tebl/BulkyModem/faceplates/BulkyModem Terminal FP3/README.md

# BulkyModem Terminal FP3
This is a faceplate, an inherently optional part of any build as it does not actually contain any active components. This faceplate mounts on the **front** of the device, and it is compatible with the following main projects:
- [BulkyModem Terminal](https://github.com/tebl/BulkyModem/tree/main/BulkyModem%20Terminal)

It currently looks like this:
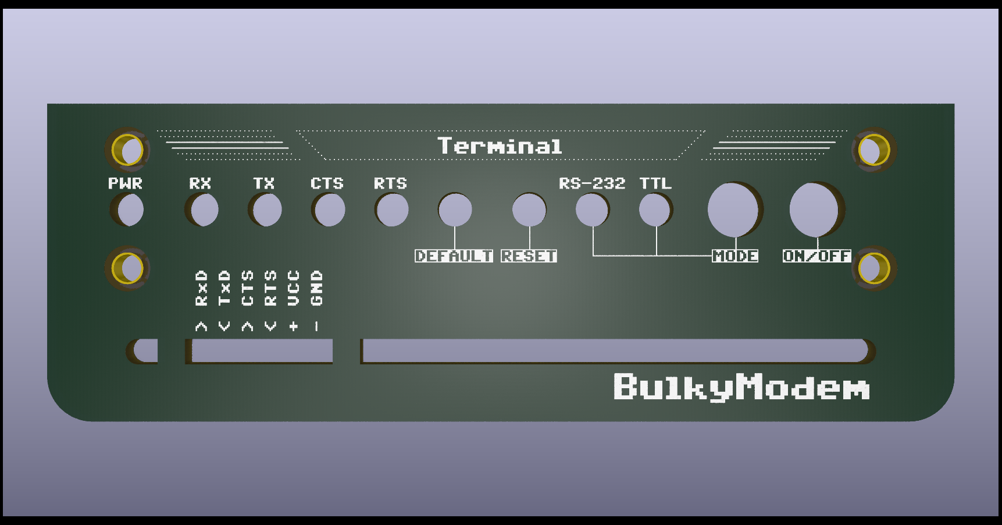
[picture p60: gallery/BulkyModem Terminal FP3.png]
Preview
