tebl/BulkyModem/gallery/20230408_013329.jpg

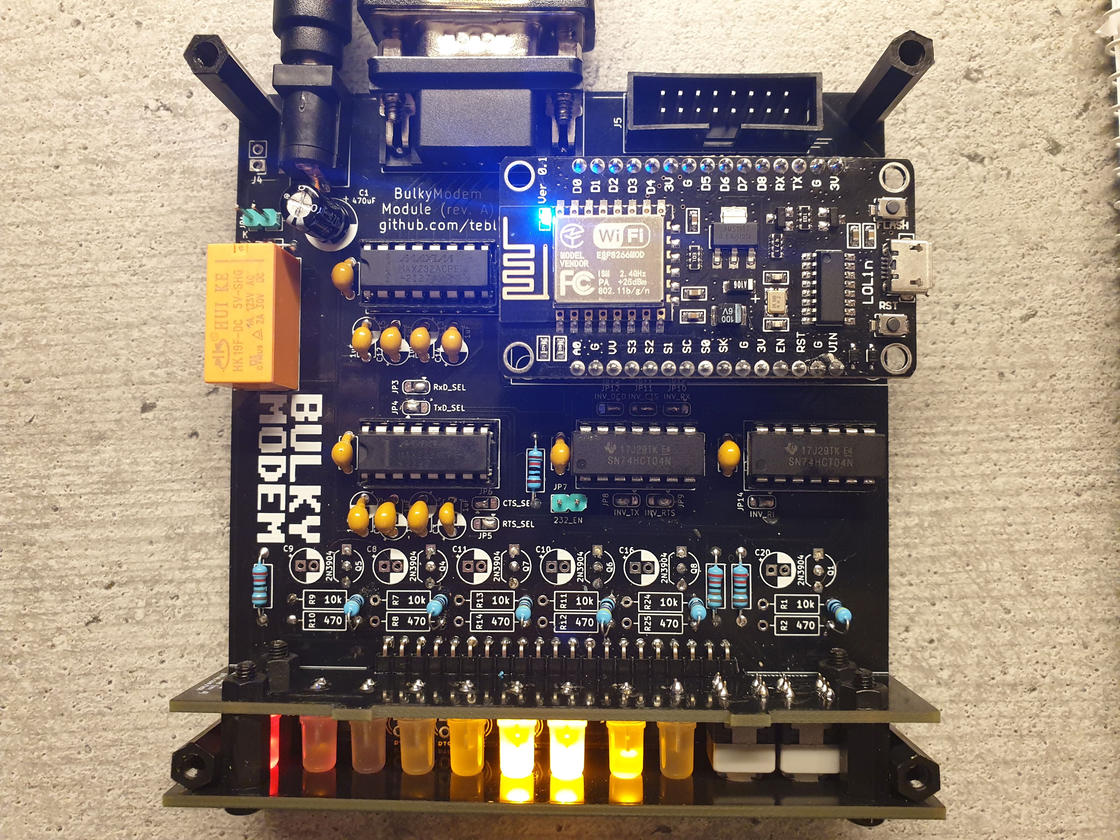
gallery/20230408_013329.jpg
