tebl/BulkyModem/gallery/20240408_024902.jpg

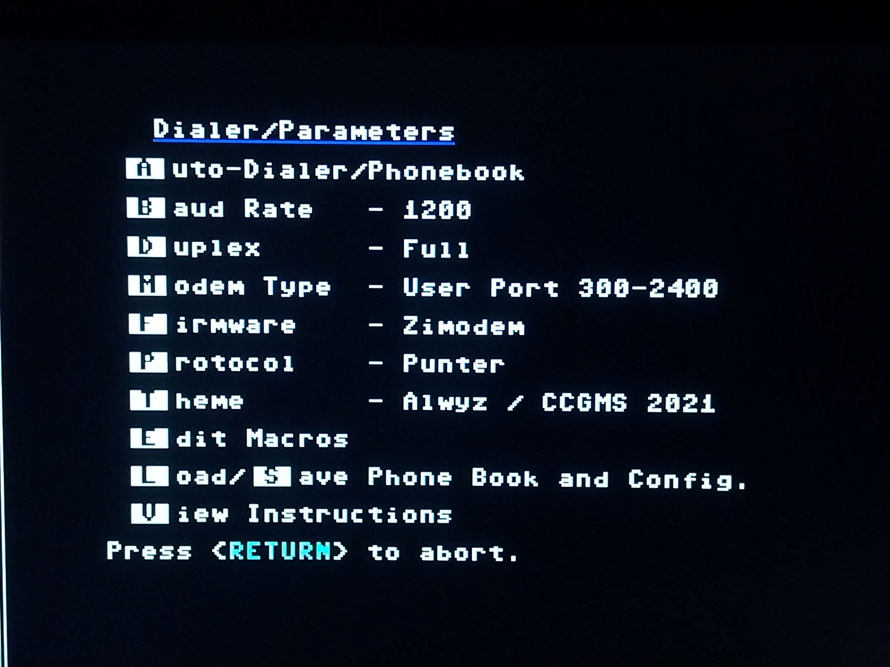
gallery/20240408_024902.jpg
