tebl/BulkyModem/gallery/20240408_025356.jpg

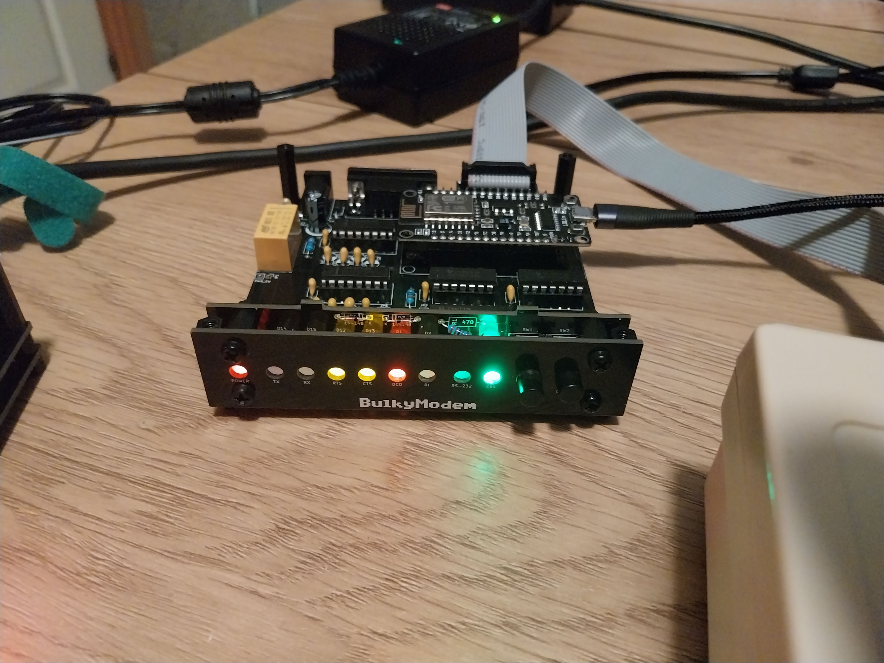
gallery/20240408_025356.jpg
