tebl/BulkyModem/gallery/20240408_030150.jpg

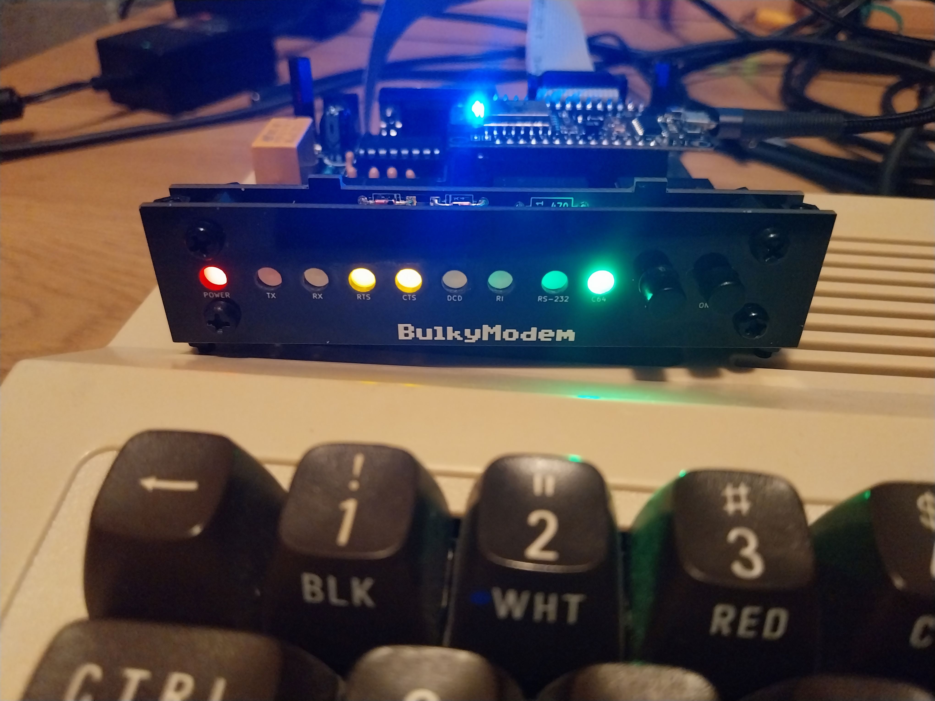
gallery/20240408_030150.jpg
