tebl/BulkyModem/gallery/20240408_030332.jpg

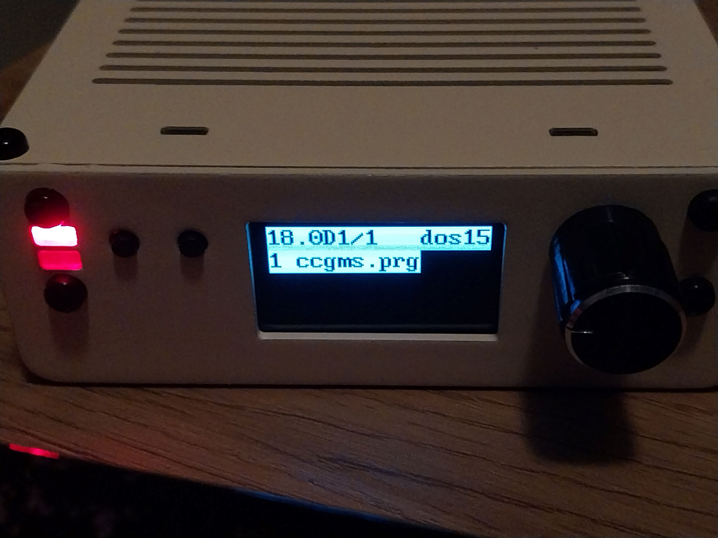
gallery/20240408_030332.jpg
