tebl/BulkyModem/gallery/20240408_030412.jpg

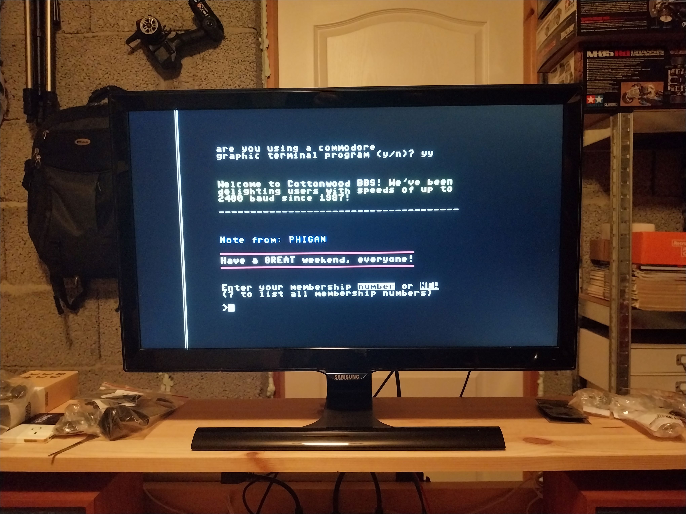
gallery/20240408_030412.jpg
