tebl/BulkyModem/gallery/20240409_003450.jpg

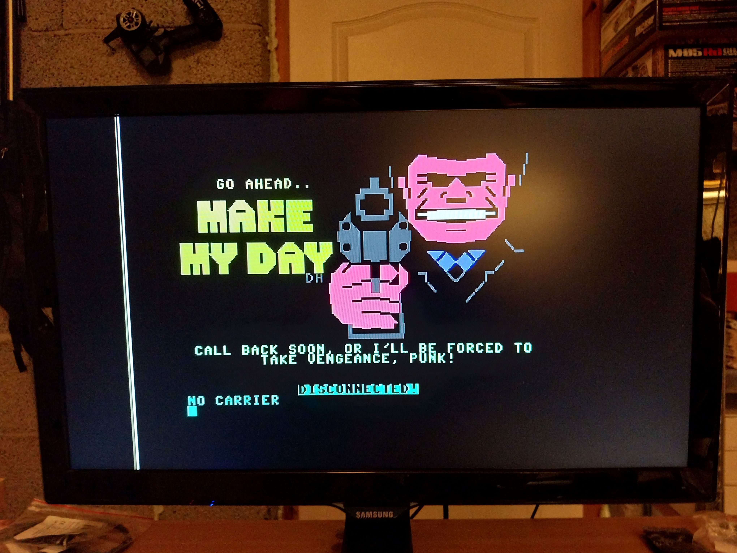
gallery/20240409_003450.jpg
