tebl/BulkyModem/gallery/20240411_001839.jpg

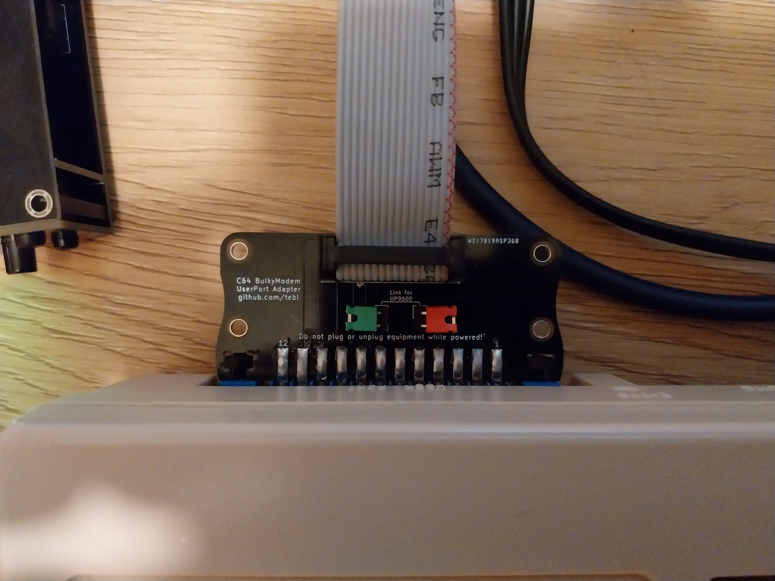
gallery/20240411_001839.jpg
