tebl/BulkyModem/gallery/20240411_020940.jpg

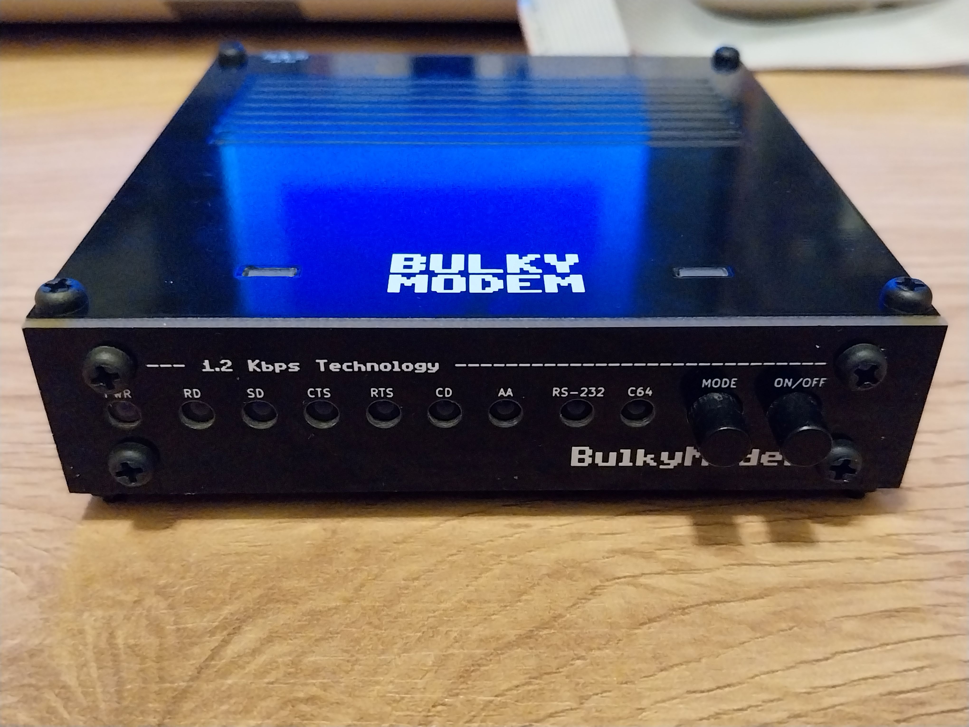
gallery/20240411_020940.jpg
