tebl/BulkyModem/gallery/20240411_020946.jpg

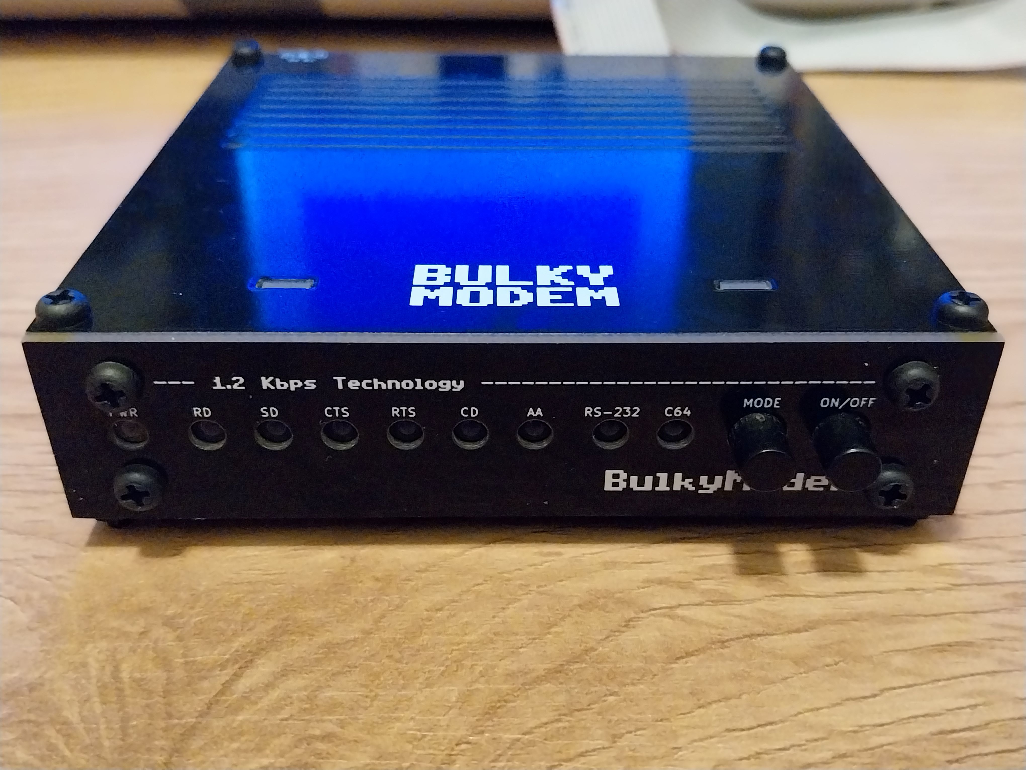
gallery/20240411_020946.jpg
