tebl/BulkyModem/gallery/20240411_021111.jpg

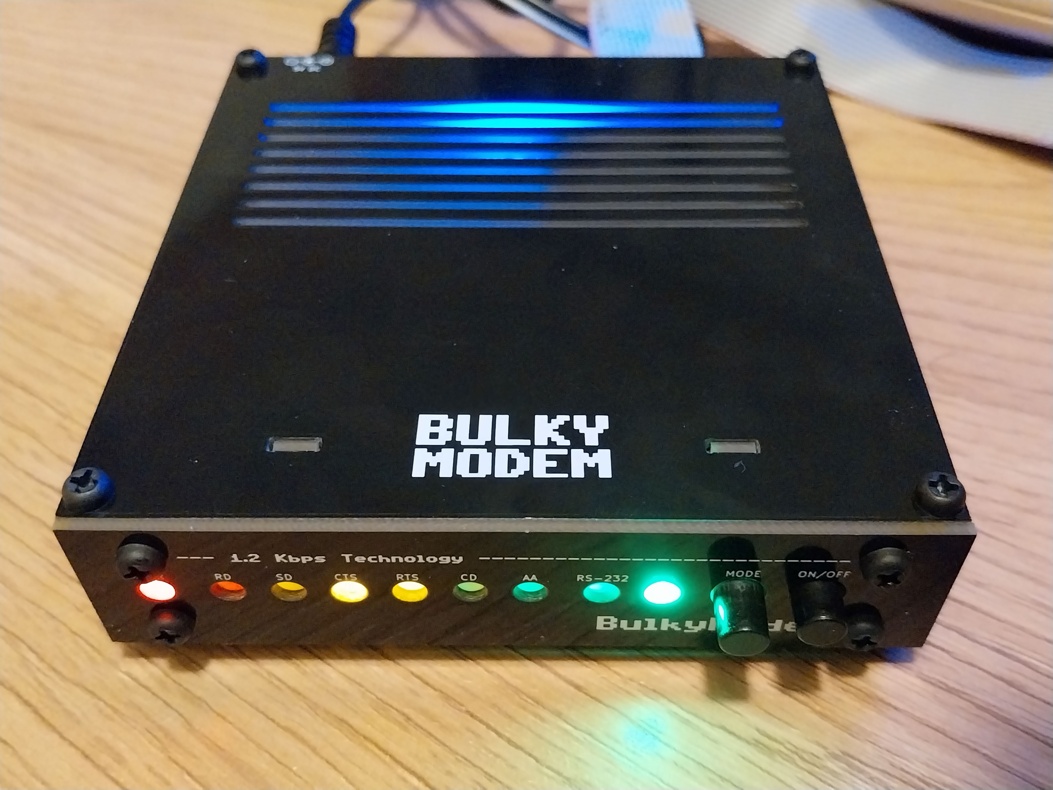
gallery/20240411_021111.jpg
