tebl/BulkyModem/gallery/20240531_021321.jpg

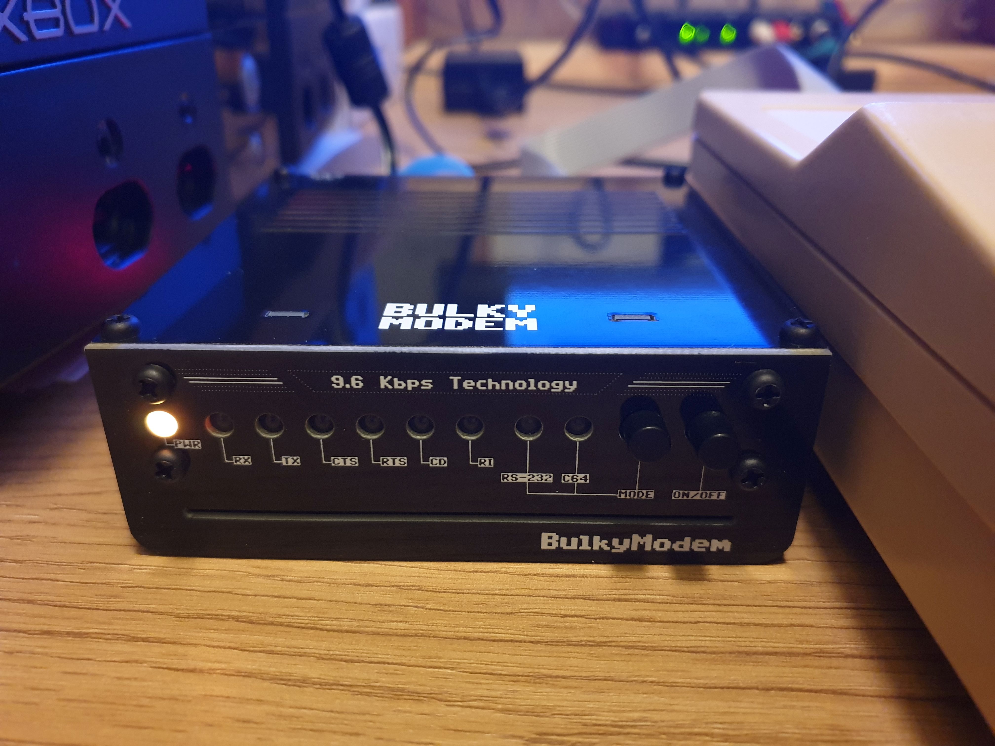
gallery/20240531_021321.jpg
