tebl/BulkyModem/gallery/20240531_021749.jpg

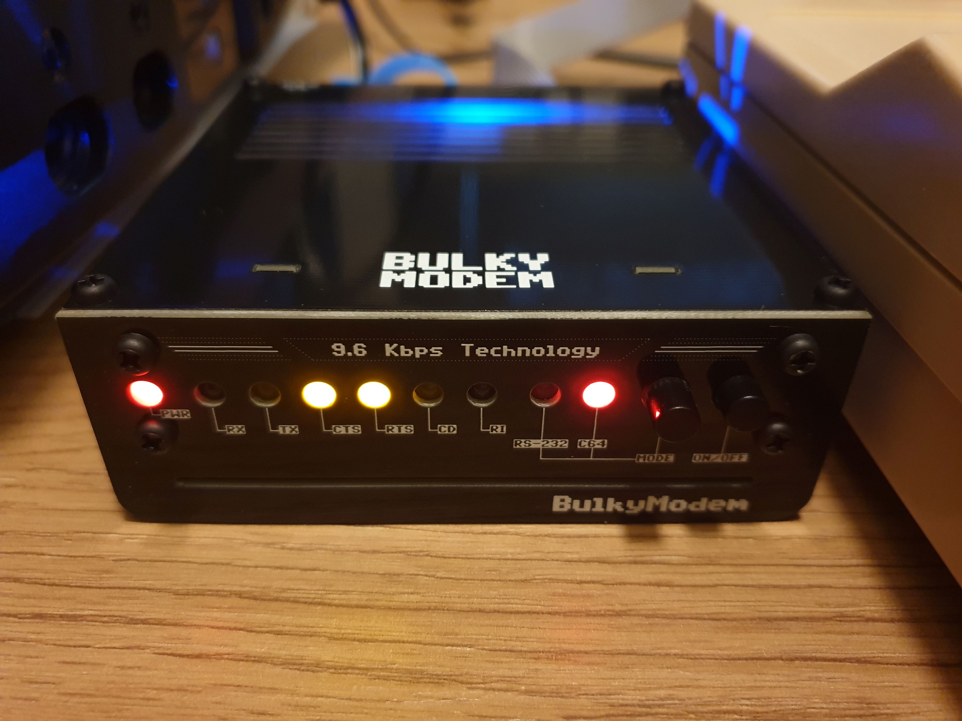
gallery/20240531_021749.jpg
