tebl/BulkyModem/gallery/20240626_021226.jpg

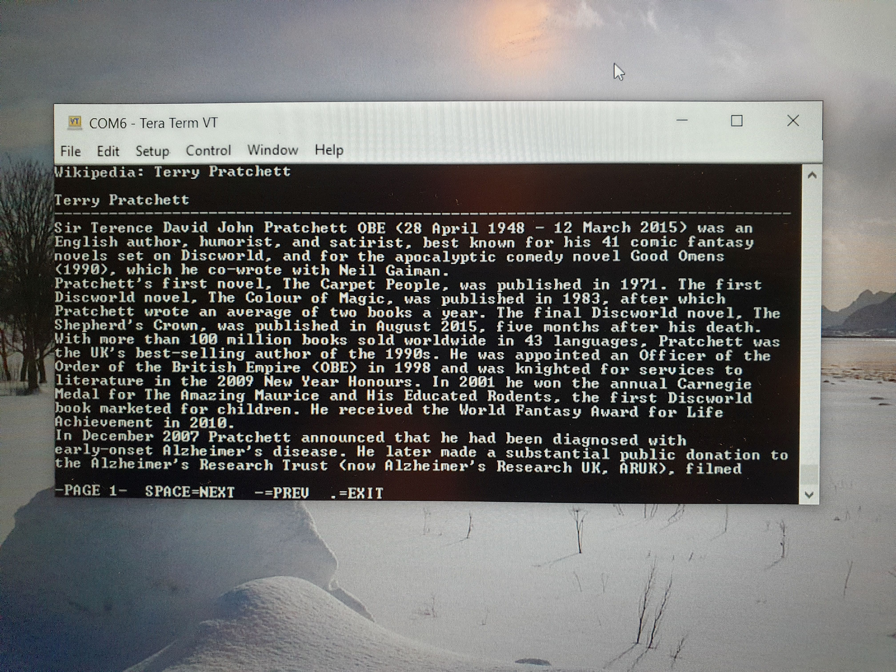
gallery/20240626_021226.jpg
