tebl/BulkyModem/gallery/20240628_021208.jpg

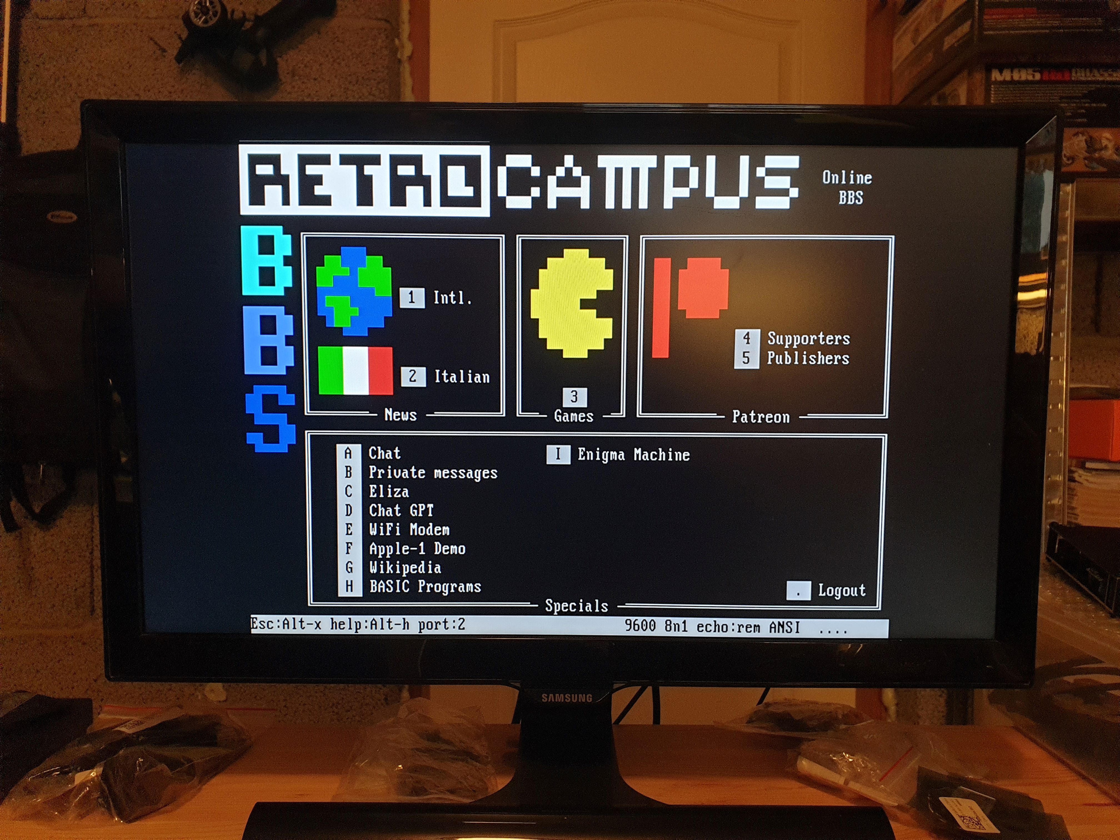
gallery/20240628_021208.jpg
