tebl/BulkyModem/gallery/20240628_021517.jpg

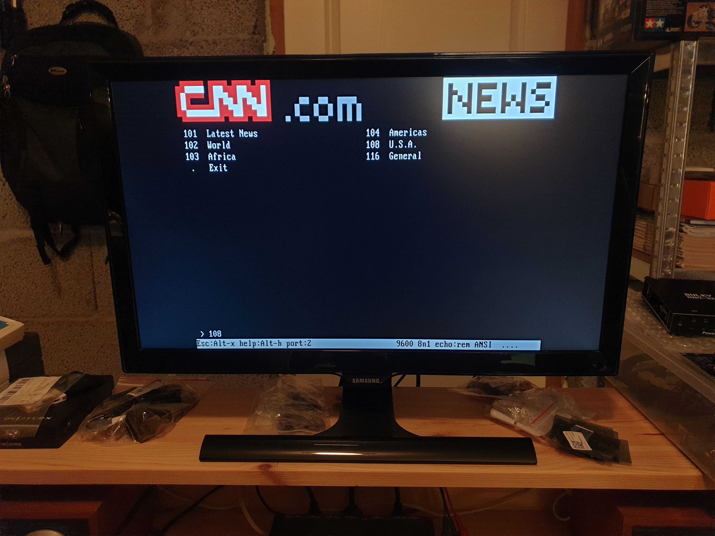
gallery/20240628_021517.jpg
