tebl/BulkyModem/gallery/20240720_025950.jpg

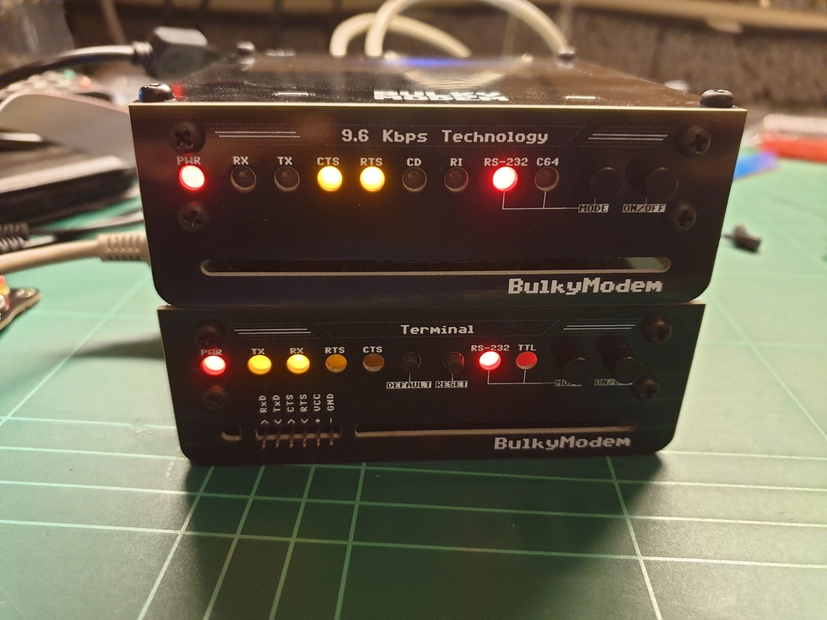
gallery/20240720_025950.jpg
