tebl/BulkyModem/gallery/20240720_035339.jpg

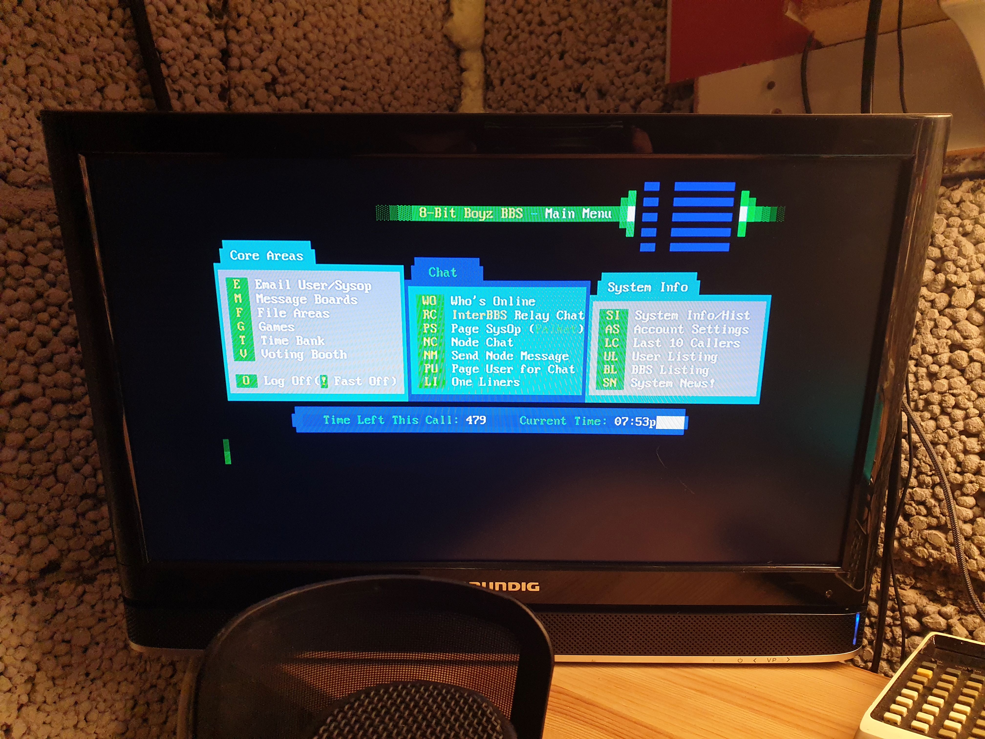
gallery/20240720_035339.jpg
