tebl/BulkyModem/gallery/20240720_035406.jpg

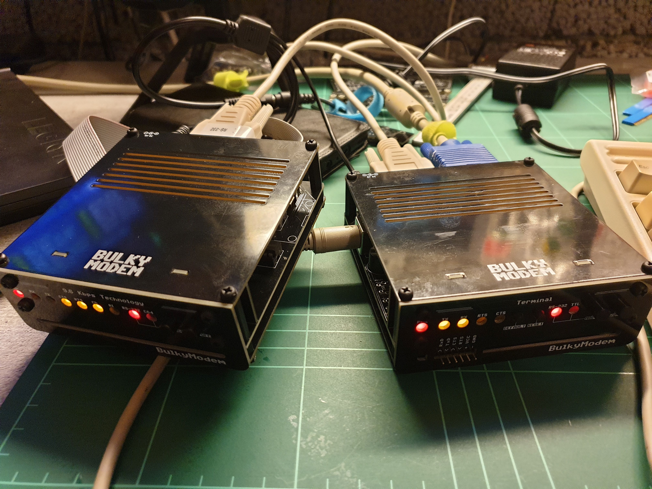
gallery/20240720_035406.jpg
