tebl/BulkyModem/gallery/20240807_004950.jpg

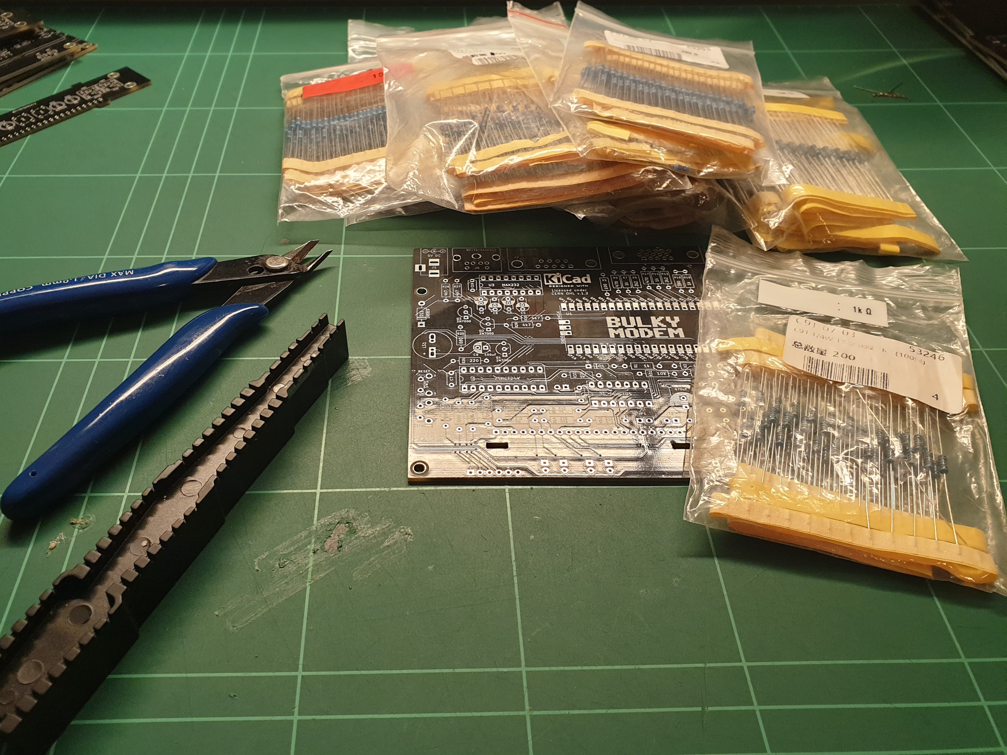
gallery/20240807_004950.jpg
