tebl/BulkyModem/gallery/20240809_001635.jpg

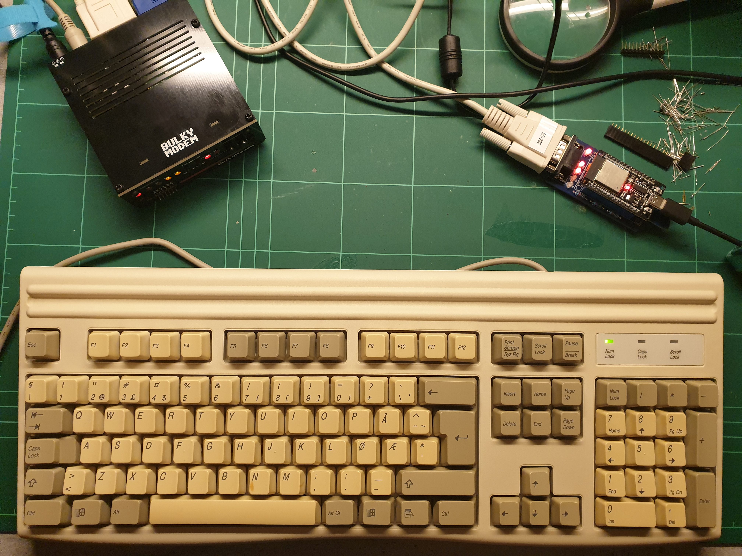
gallery/20240809_001635.jpg
