tebl/BulkyModem/gallery/BulkyModem FP1.jpg

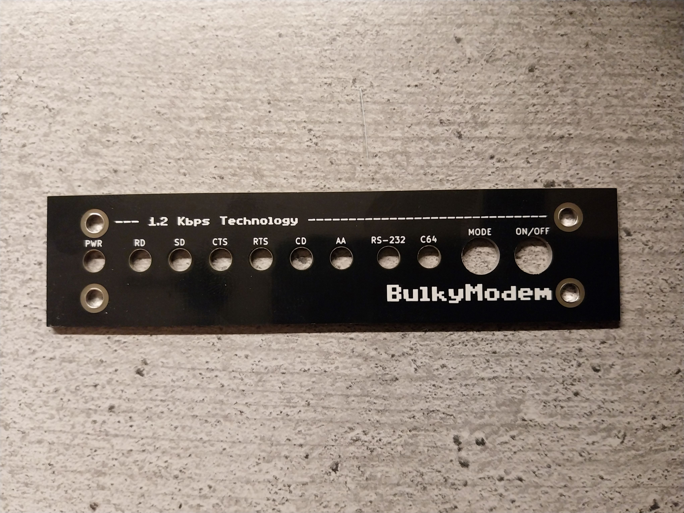
gallery/BulkyModem FP1.jpg
