tebl/BulkyModem/gallery/BulkyModem FP1.png

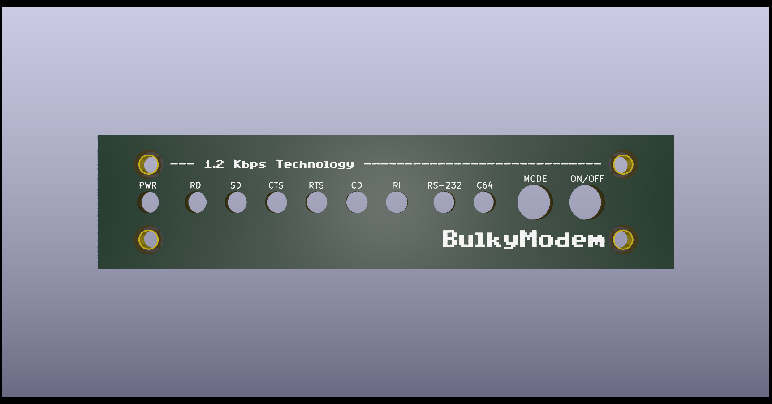
gallery/BulkyModem FP1.png
