tebl/BulkyModem/gallery/BulkyModem FP3.jpg

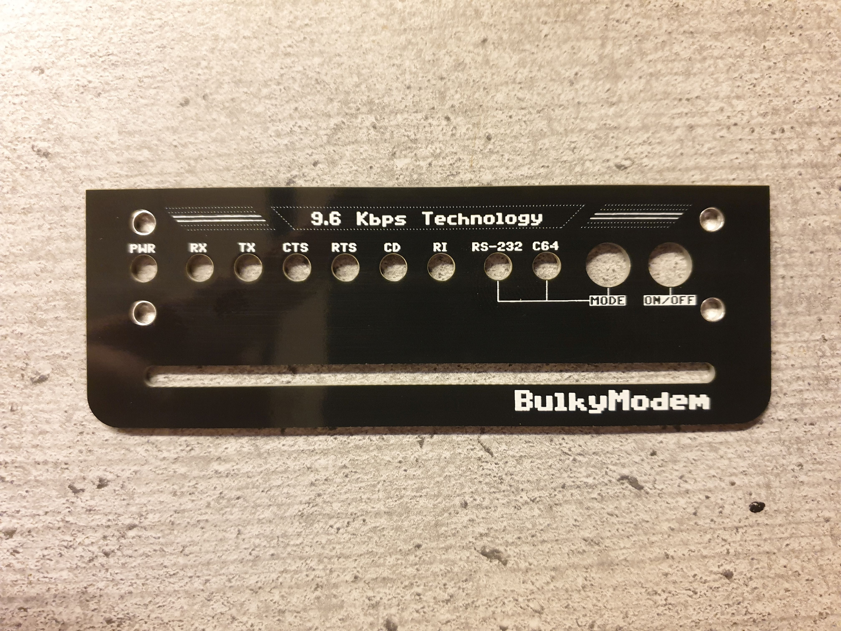
gallery/BulkyModem FP3.jpg
