tebl/BulkyModem/gallery/BulkyModem Module Audio.png

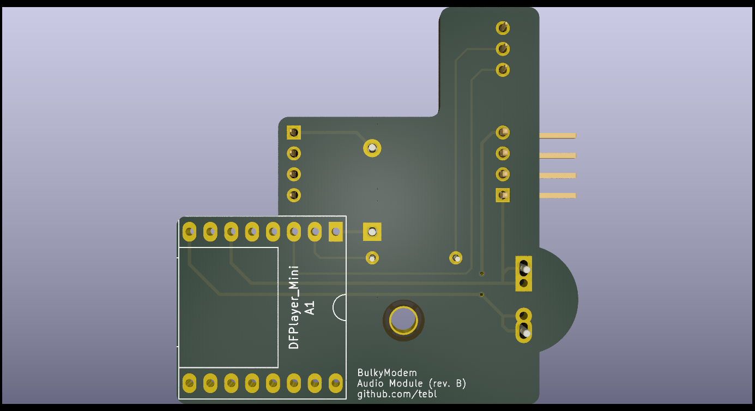
gallery/BulkyModem Module Audio.png
