tebl/BulkyModem/gallery/BulkyModem Module.png

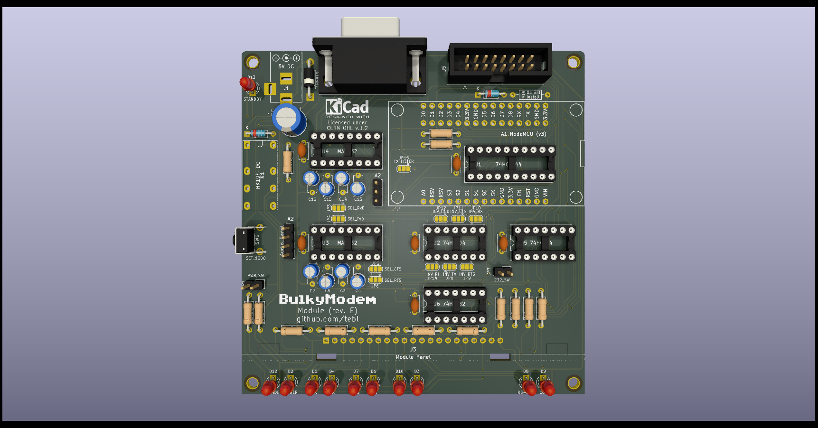
gallery/BulkyModem Module.png
