tebl/BulkyModem/gallery/BulkyModem Terminal FA1.jpg

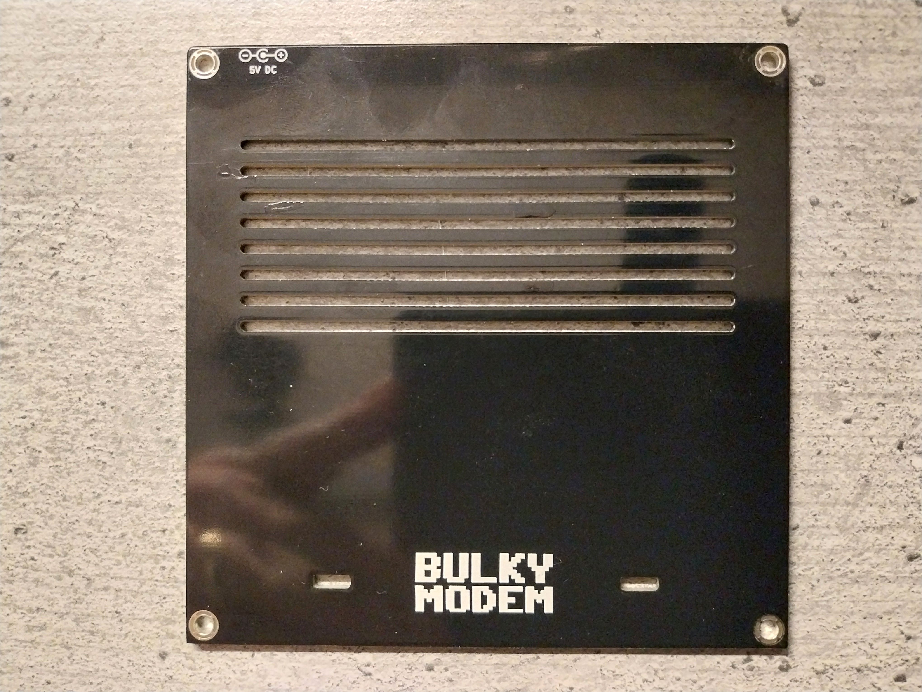
gallery/BulkyModem Terminal FA1.jpg
