tebl/BulkyModem/gallery/BulkyModem Terminal FP3.jpg

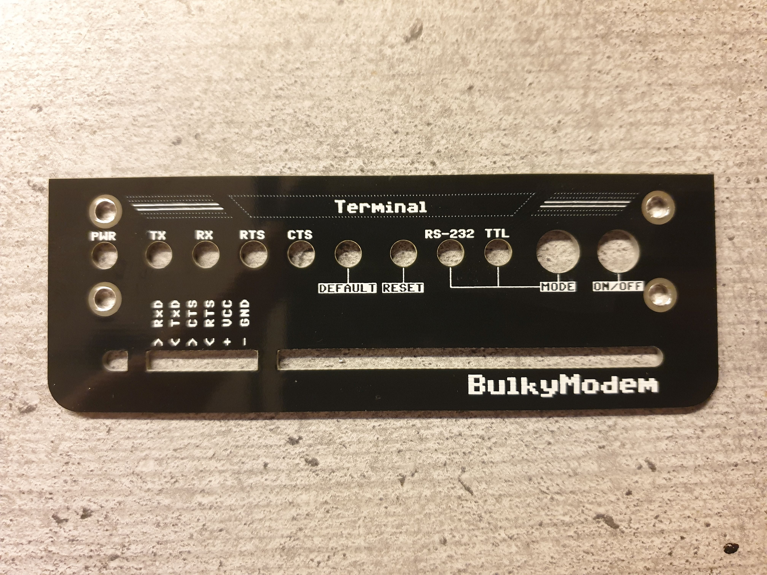
gallery/BulkyModem Terminal FP3.jpg
