tebl/BulkyModem/gallery/BulkyModem Terminal Panel.png

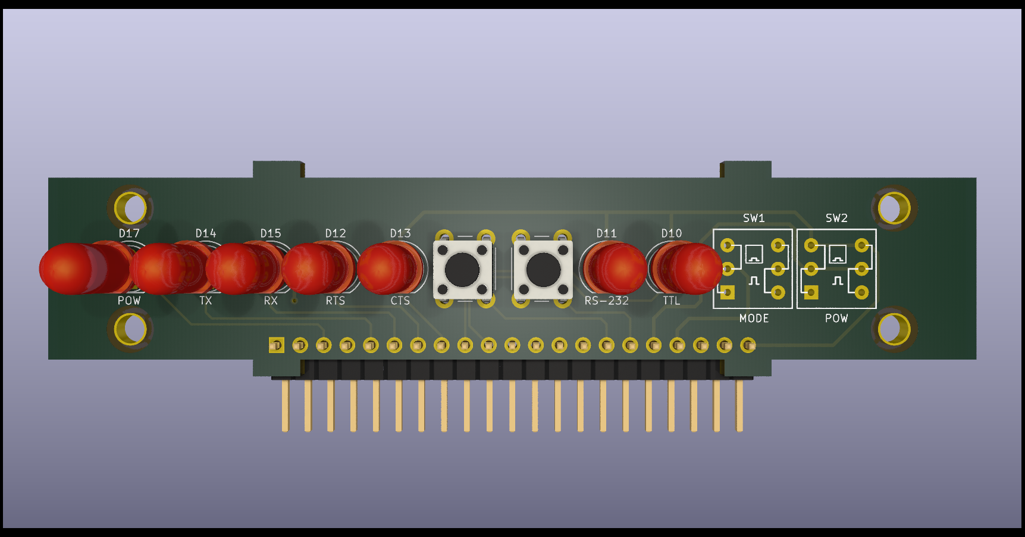
gallery/BulkyModem Terminal Panel.png
