tebl/BulkyModem/gallery/BulkyModem Terminal.png

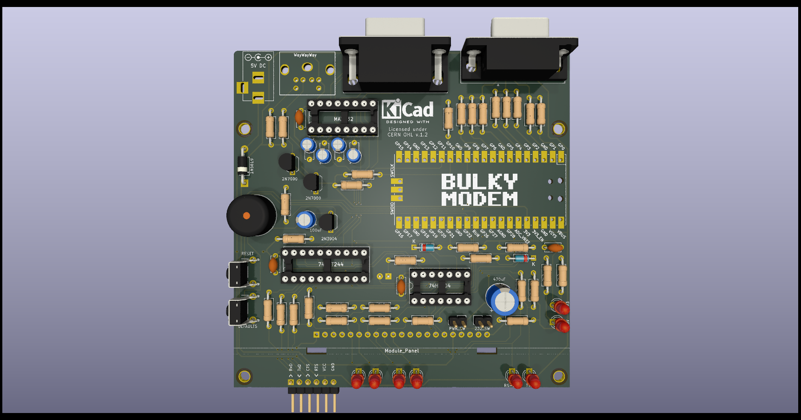
gallery/BulkyModem Terminal.png
