tebl/BulkyModem/gallery/BulkyModem UserPort Adapter.jpg

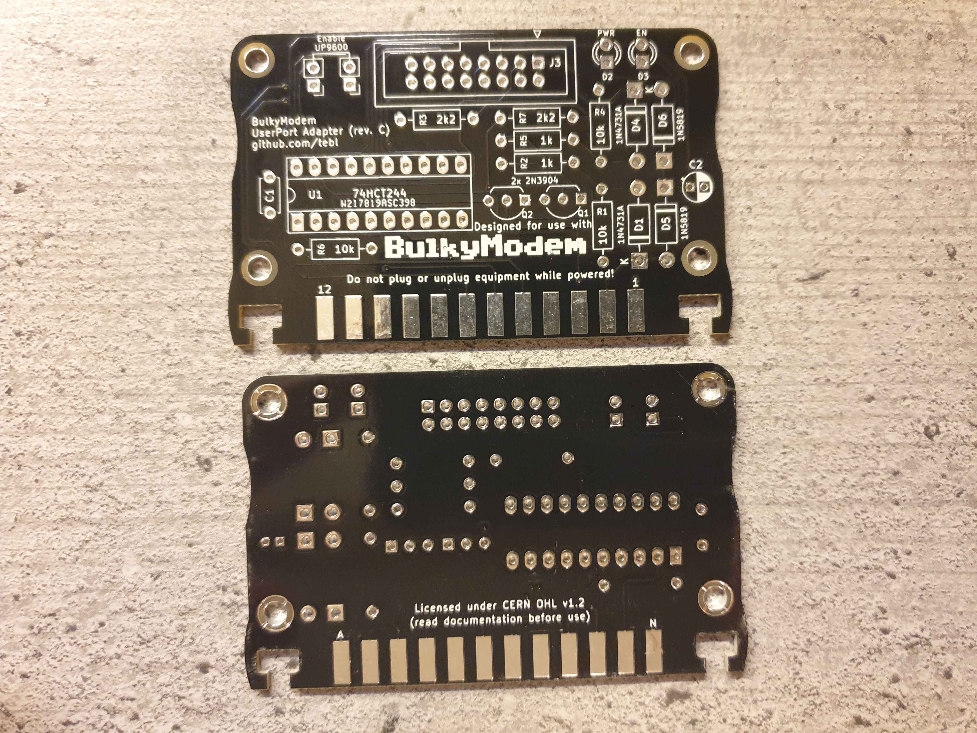
gallery/BulkyModem UserPort Adapter.jpg
