tebl/BulkyModem/gallery/BulkyModem UserPort Adapter.png

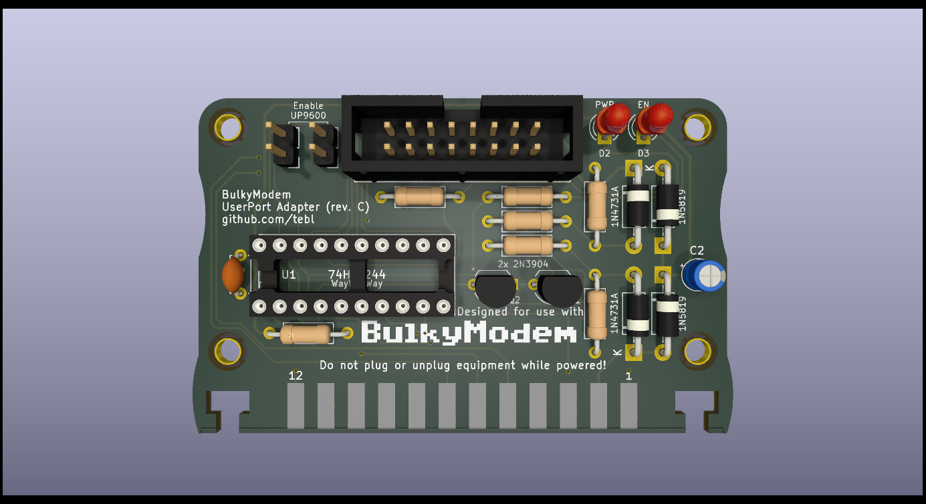
gallery/BulkyModem UserPort Adapter.png
