tebl/BulkyModem/gallery/BulkyModem-32 Mini.png

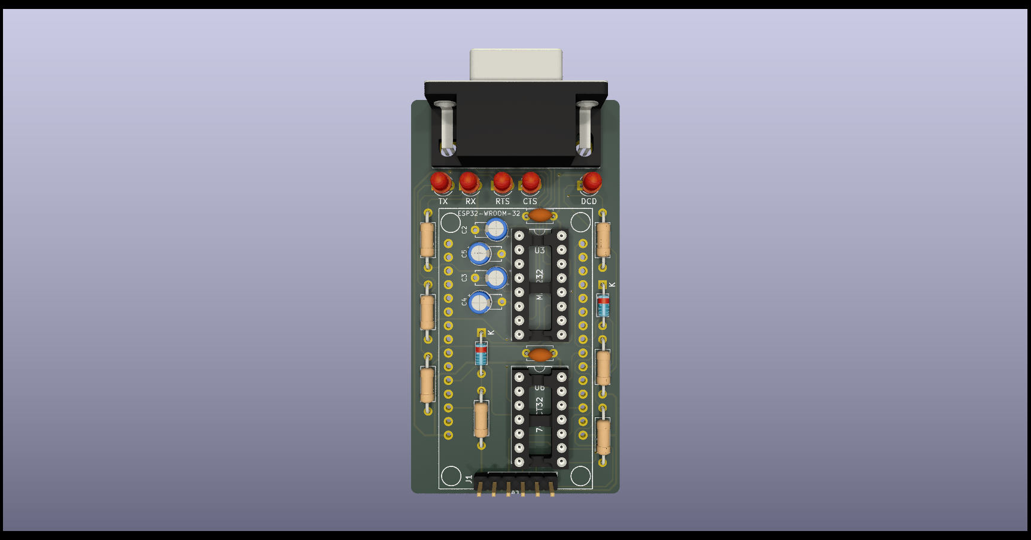
gallery/BulkyModem-32 Mini.png
