tebl/BulkyModem/gallery/BulkyModem-32 Module.png

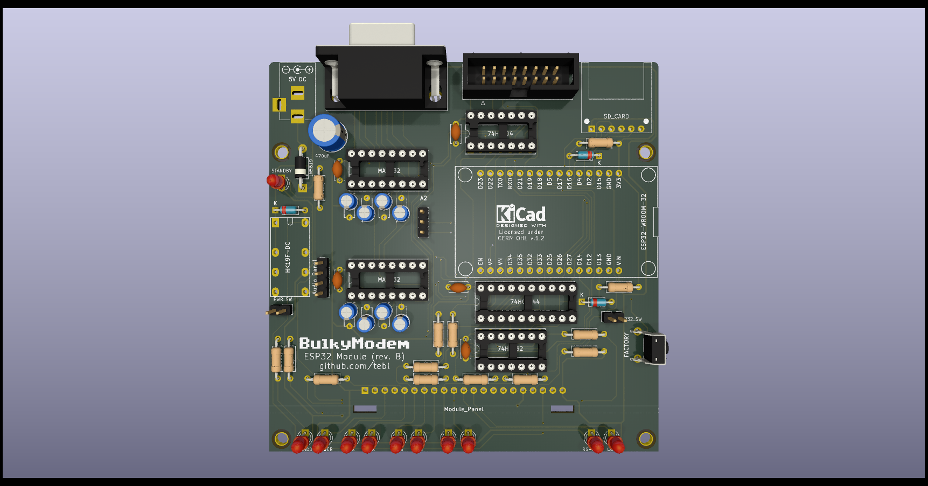
gallery/BulkyModem-32 Module.png
