tebl/BulkyModem/gallery/VideoCapture_20240408-031921.jpg

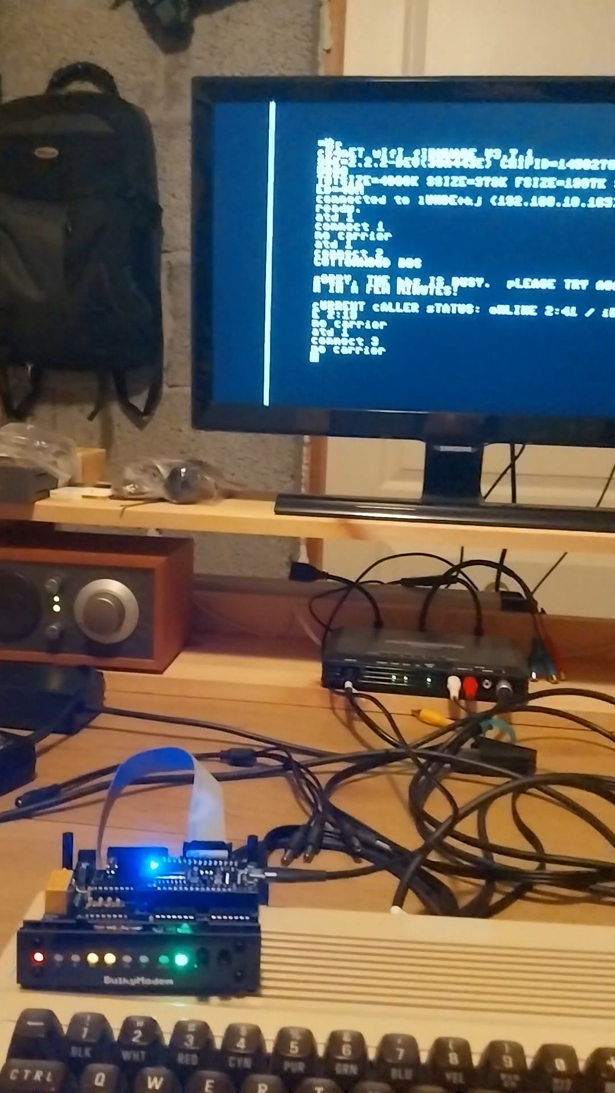
gallery/VideoCapture_20240408-031921.jpg
