tebl/BulkyModem/gallery/build/mini32_rs232/002.jpg

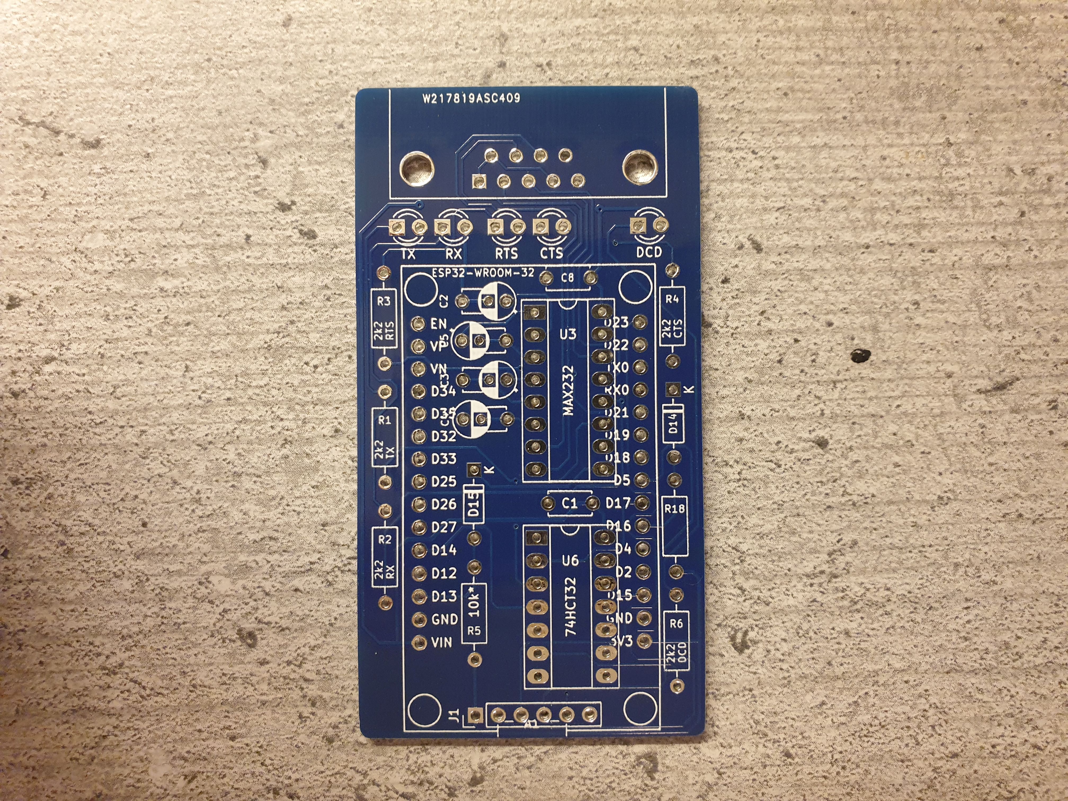
gallery/build/mini32_rs232/002.jpg
