tebl/BulkyModem/gallery/build/mini32_rs232/006.jpg

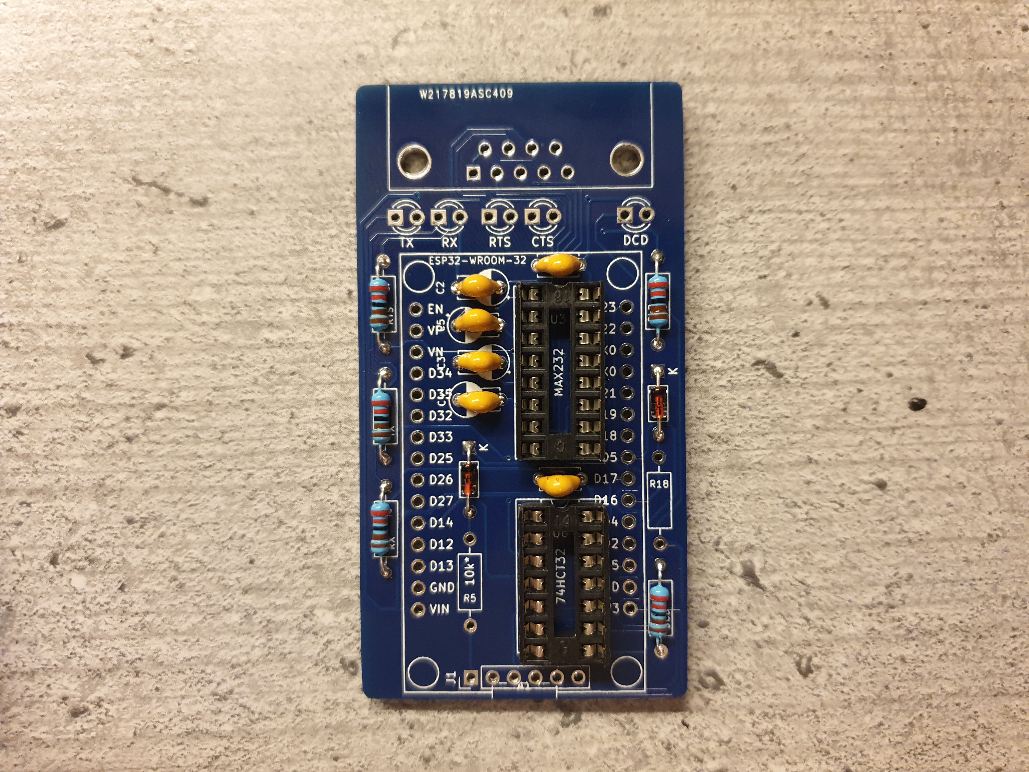
gallery/build/mini32_rs232/006.jpg
