tebl/BulkyModem/gallery/build/mini32_rs232/007.jpg

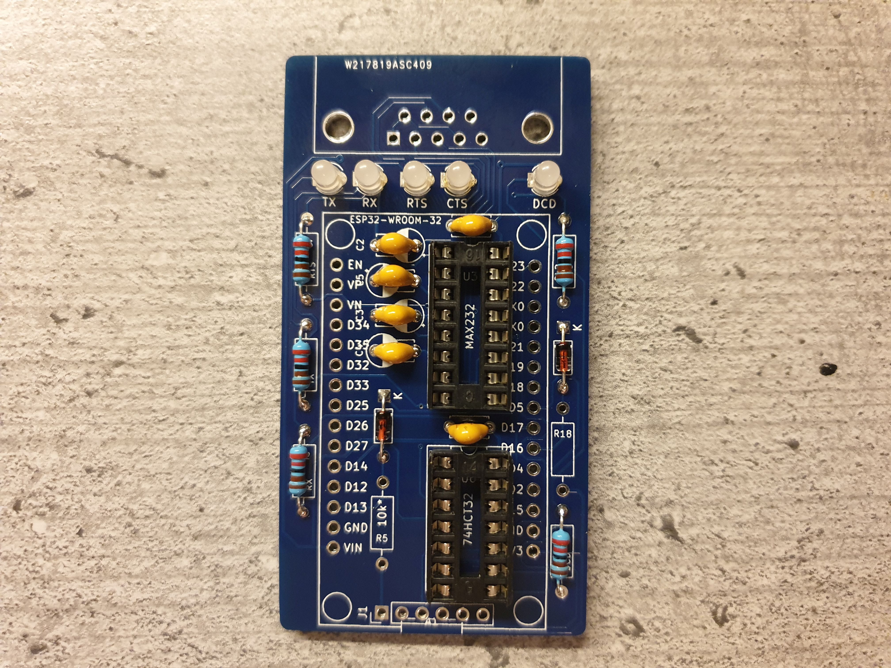
gallery/build/mini32_rs232/007.jpg
