tebl/BulkyModem/gallery/build/mini32_rs232/008.jpg

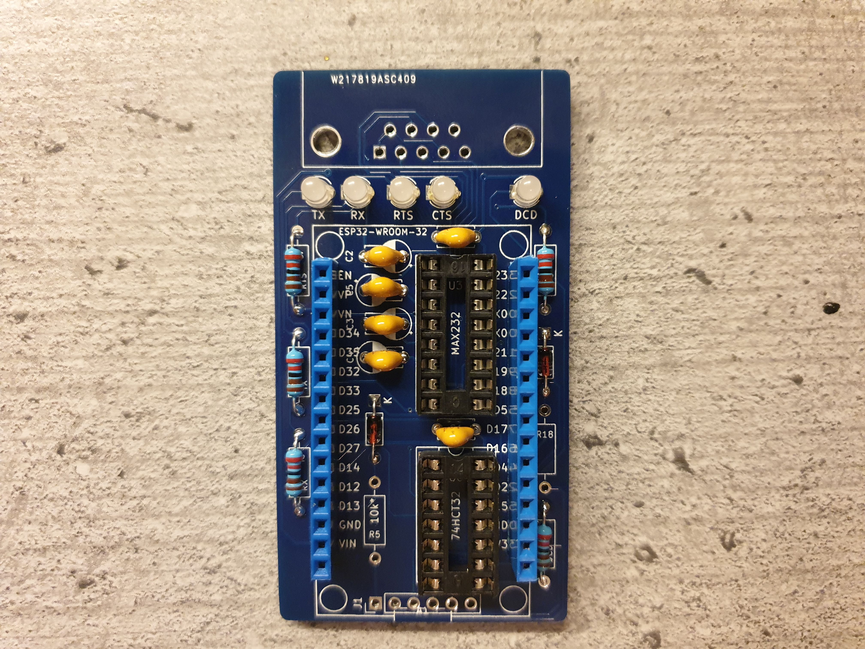
gallery/build/mini32_rs232/008.jpg
