tebl/BulkyModem/gallery/build/mini32_rs232/009.jpg

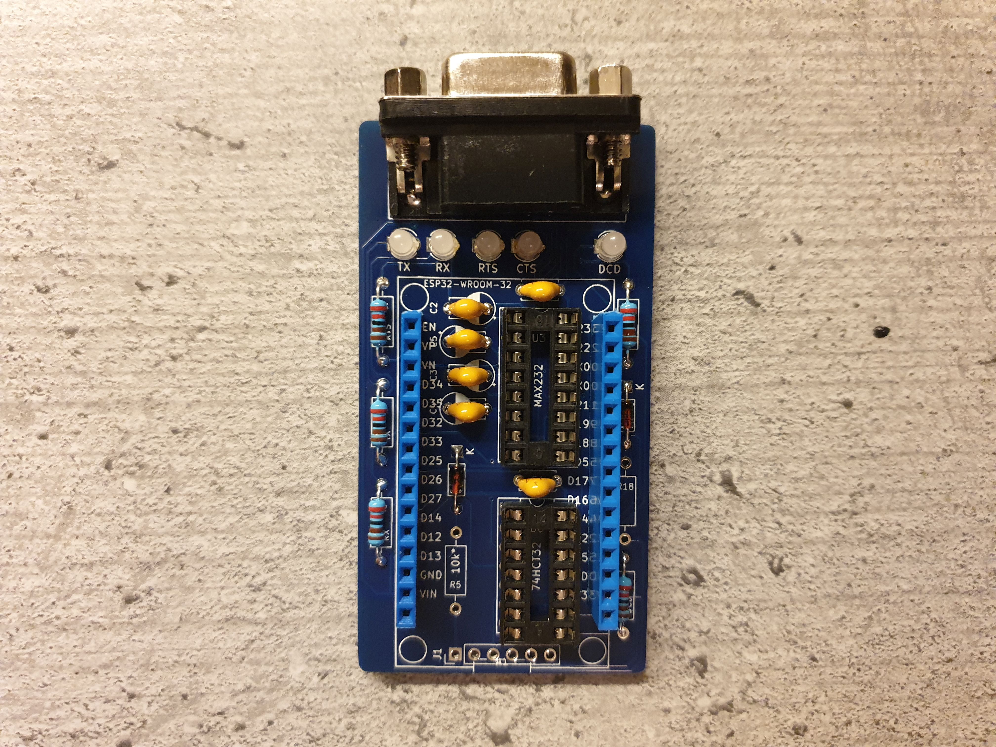
gallery/build/mini32_rs232/009.jpg
