tebl/BulkyModem/gallery/build/panel_b/001.jpg

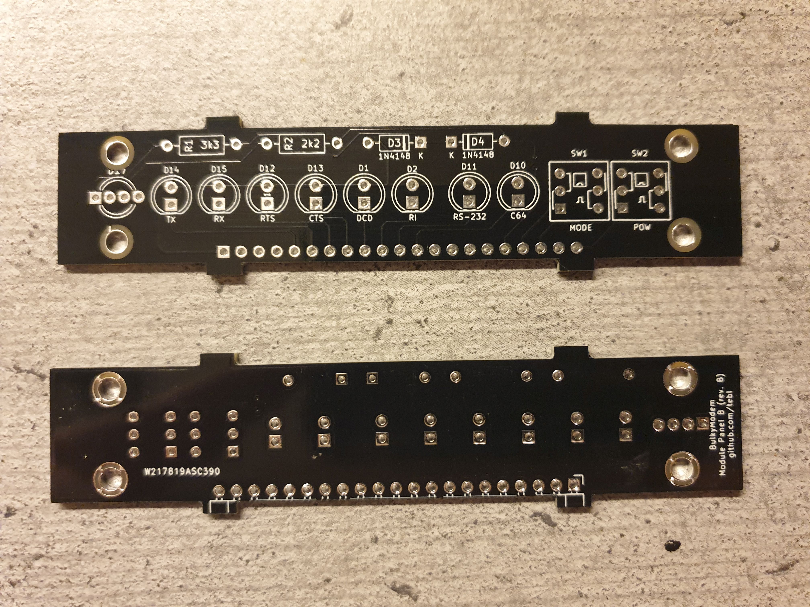
gallery/build/panel_b/001.jpg
