tebl/BulkyModem/gallery/build/panel_b/002.jpg

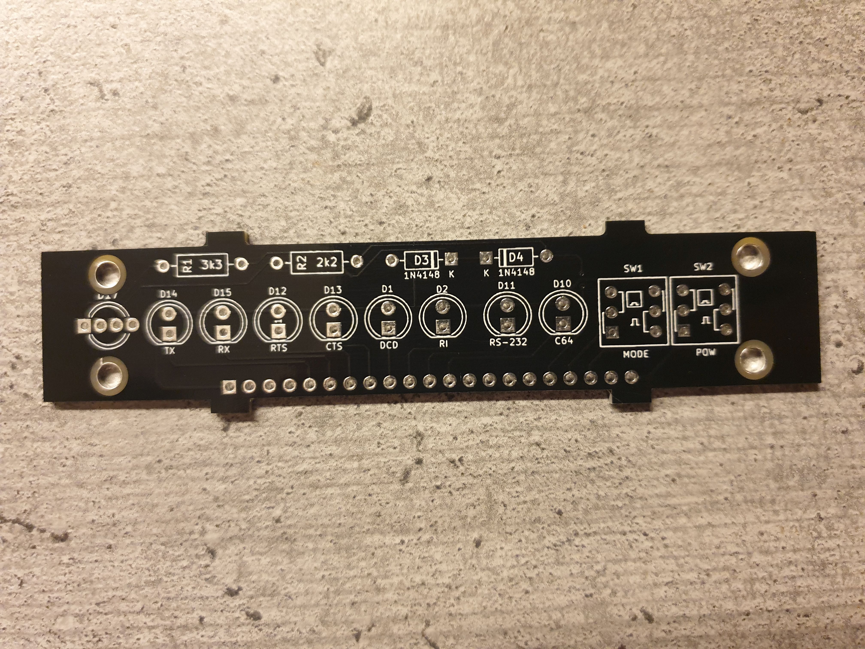
gallery/build/panel_b/002.jpg
