tebl/BulkyModem/gallery/build/panel_b/003.jpg

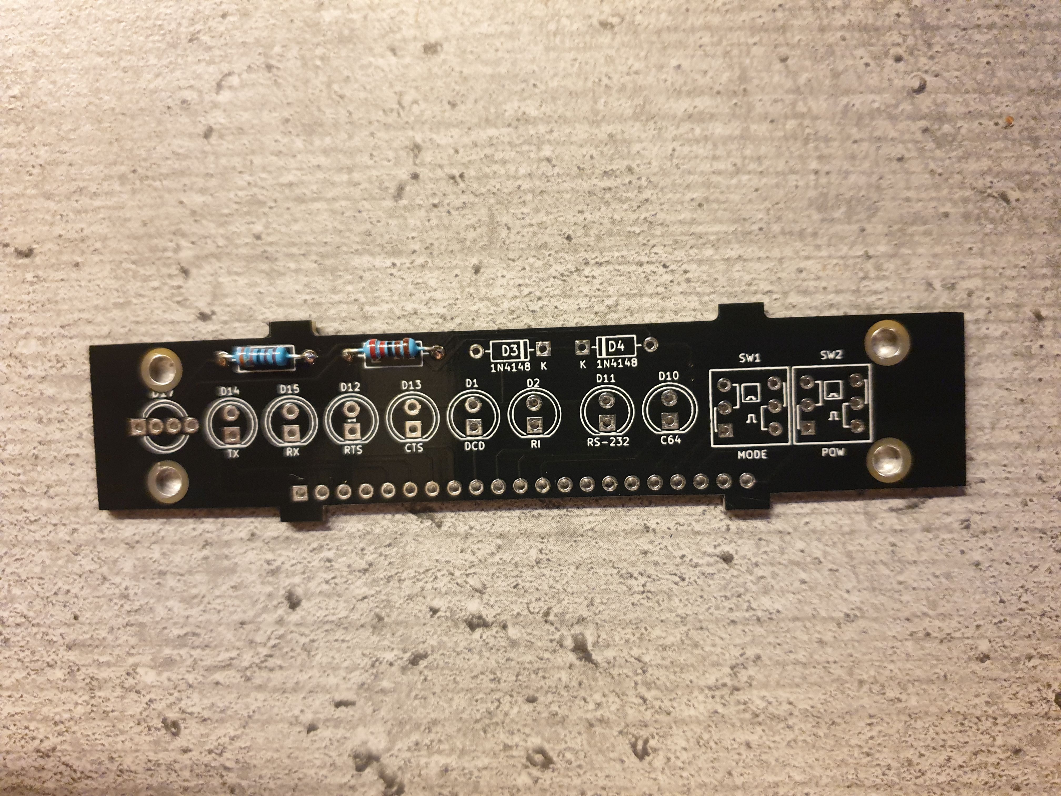
gallery/build/panel_b/003.jpg
