tebl/BulkyModem/gallery/build/panel_b/004.jpg

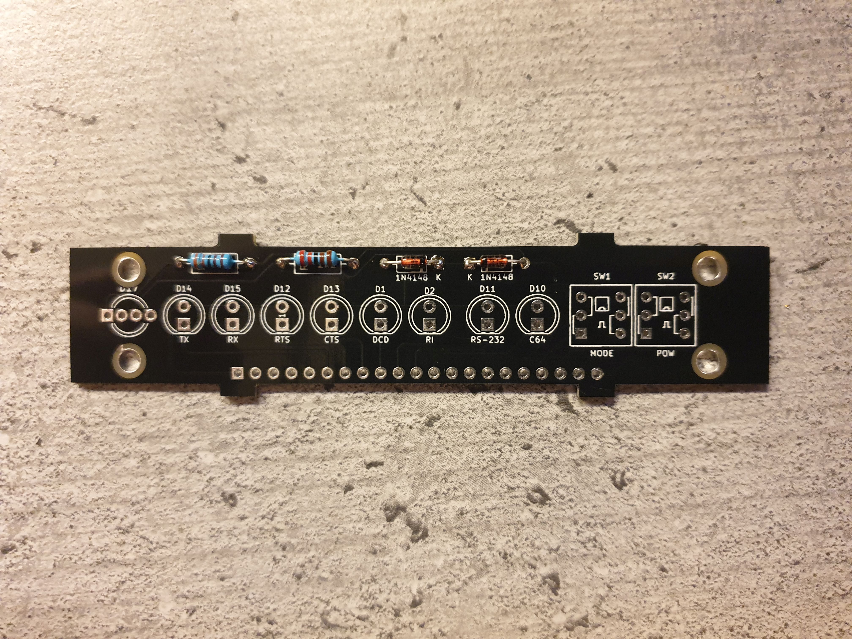
gallery/build/panel_b/004.jpg
