tebl/BulkyModem/gallery/build/panel_b/005.jpg

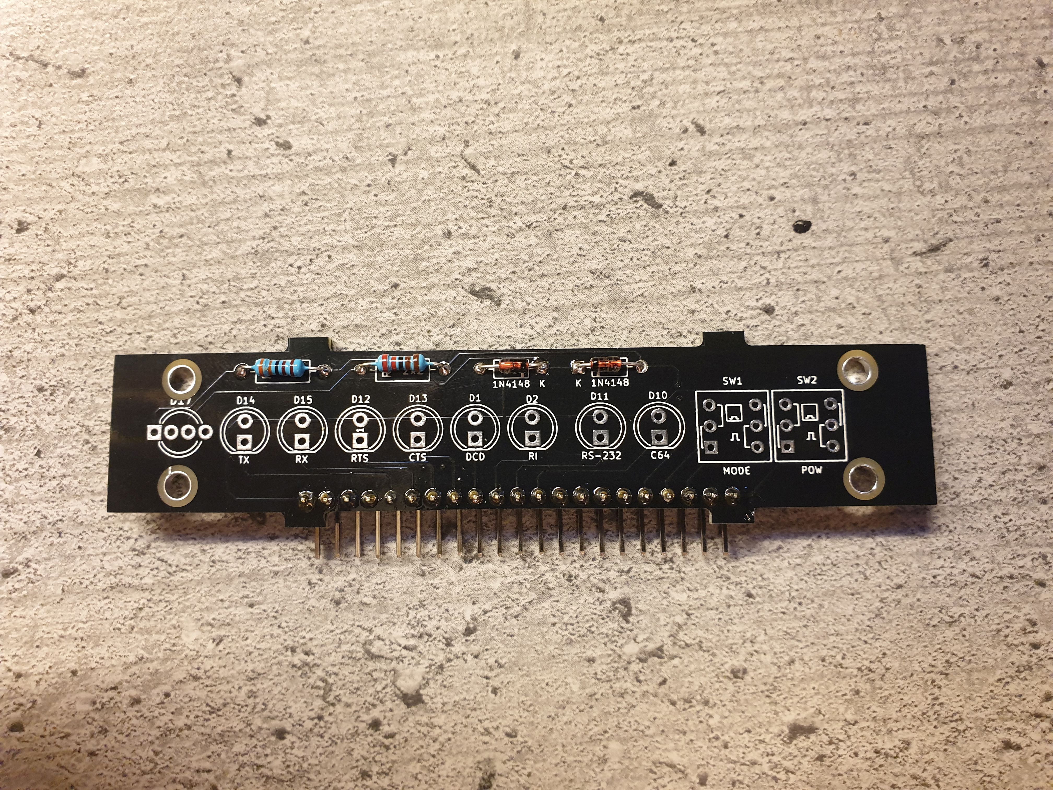
gallery/build/panel_b/005.jpg
