tebl/BulkyModem/gallery/build/panel_b/010.jpg

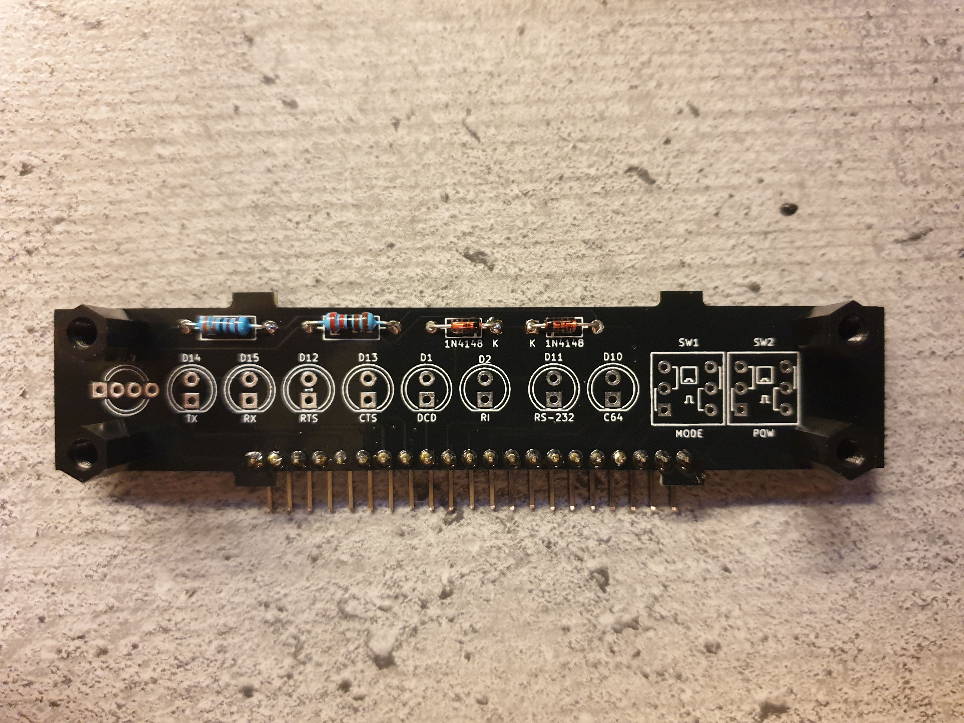
gallery/build/panel_b/010.jpg
