tebl/BulkyModem/gallery/build/panel_b/011.jpg

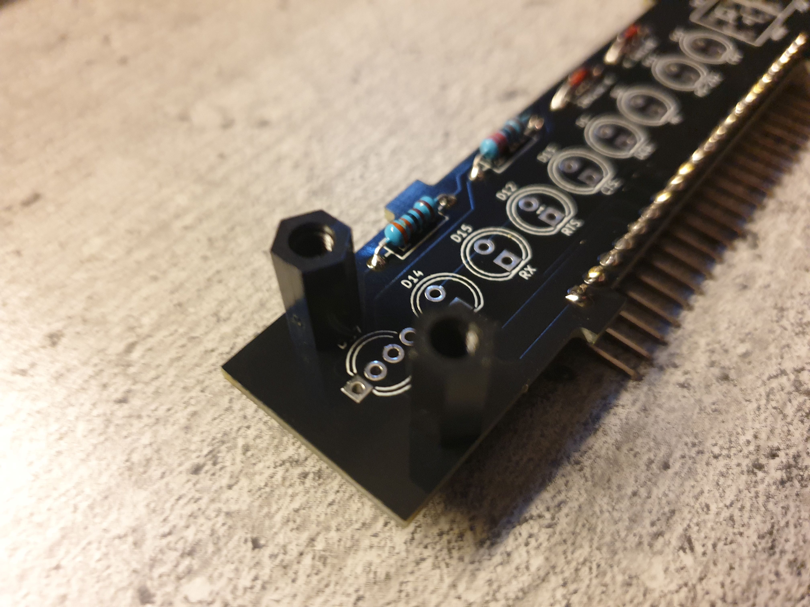
gallery/build/panel_b/011.jpg
