tebl/BulkyModem/gallery/build/panel_b/012.jpg

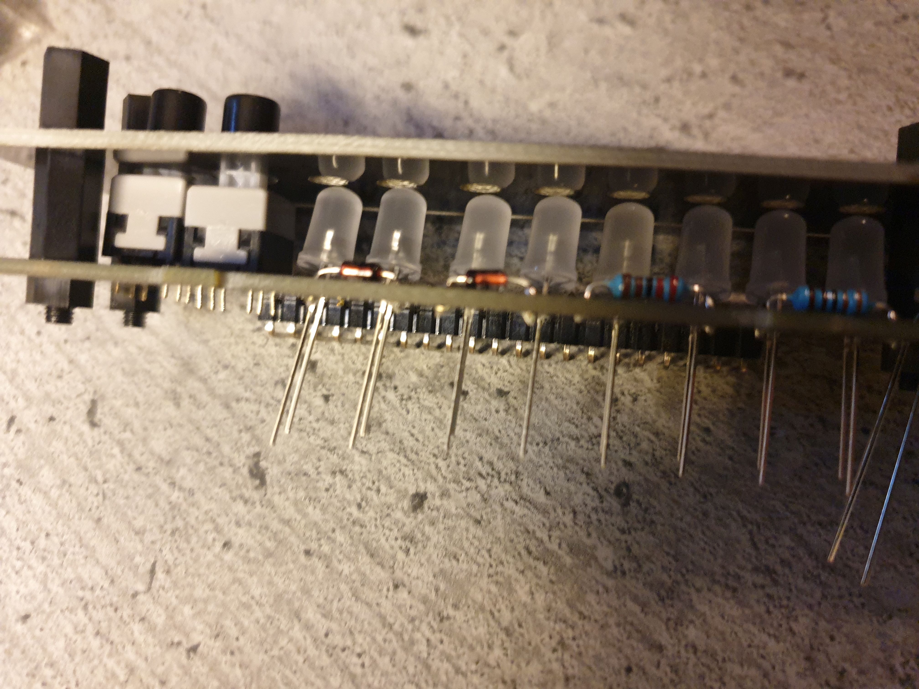
gallery/build/panel_b/012.jpg
