tebl/BulkyModem/gallery/build/panel_b/014.jpg

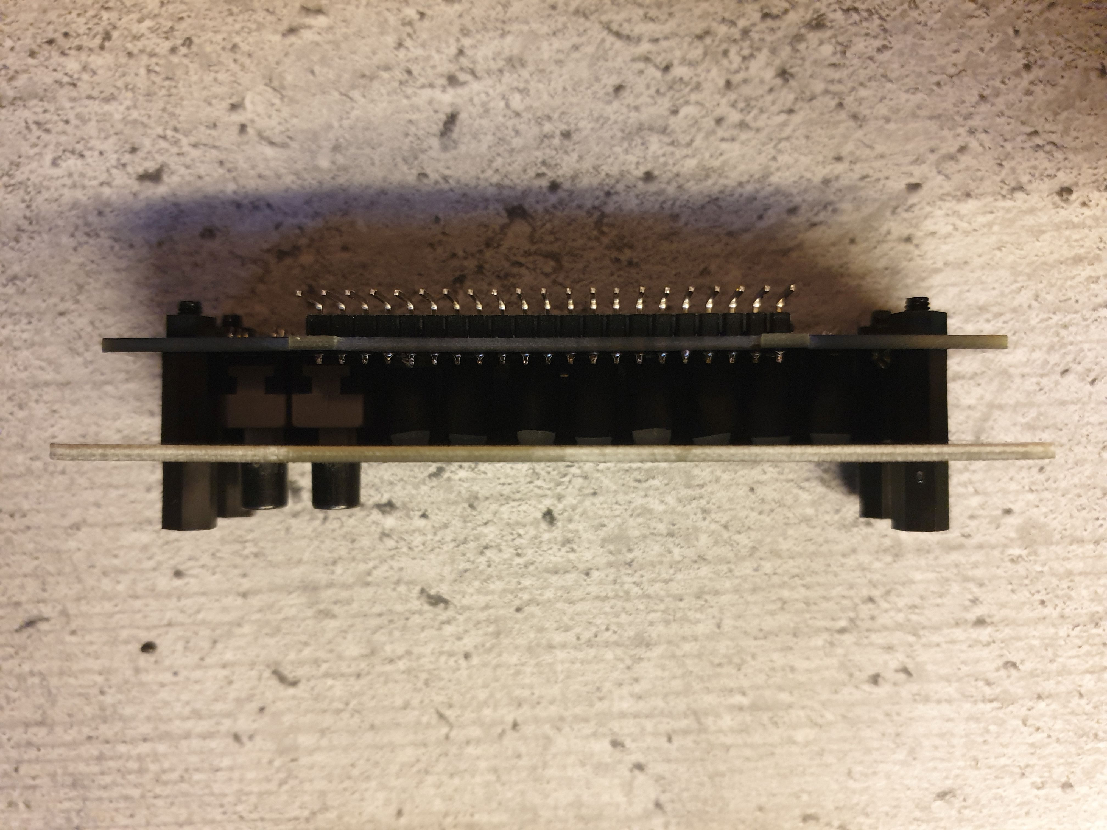
gallery/build/panel_b/014.jpg
