tebl/BulkyModem/gallery/build/panel_b/015.jpg

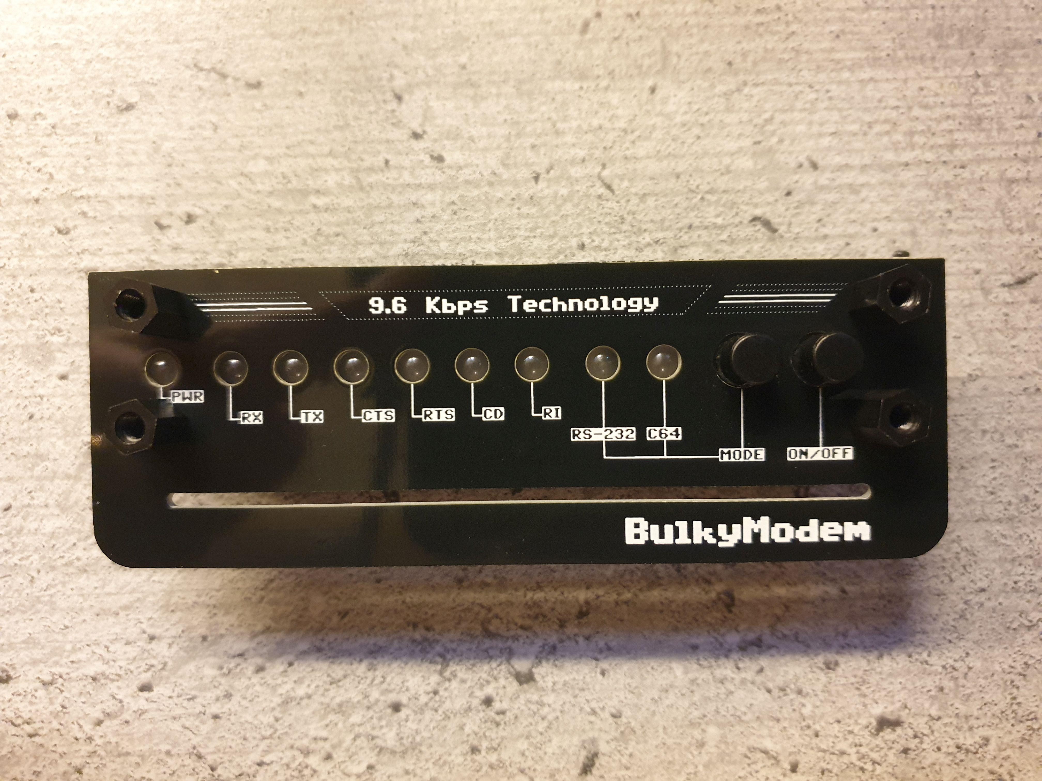
gallery/build/panel_b/015.jpg
