tebl/BulkyModem/gallery/build/terminal/003.jpg

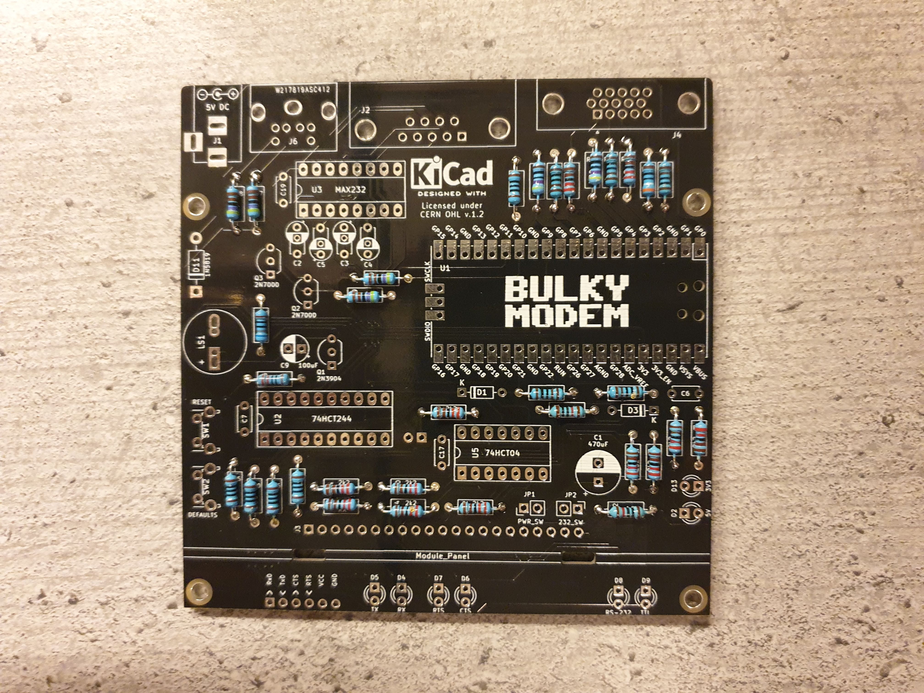
gallery/build/terminal/003.jpg
