tebl/BulkyModem/gallery/build/terminal/004.jpg

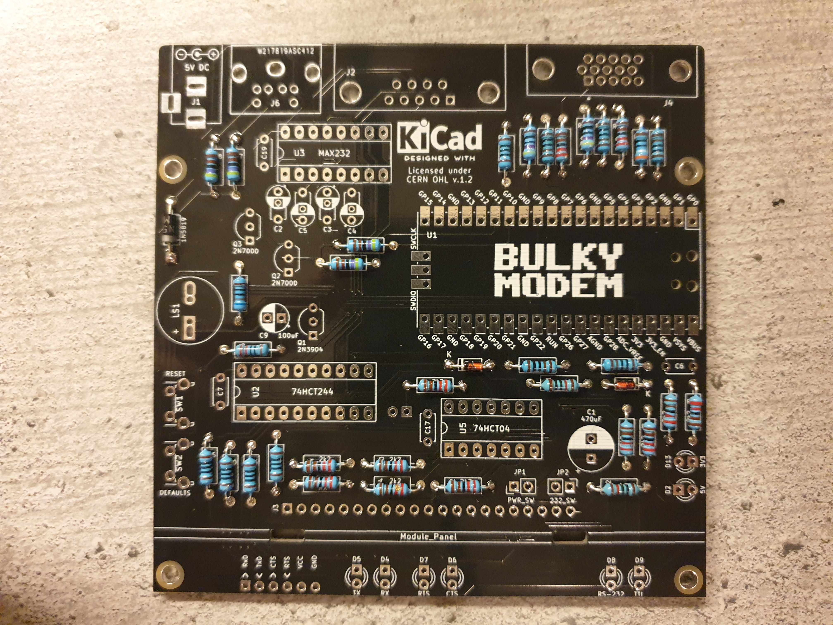
gallery/build/terminal/004.jpg
