tebl/BulkyModem/gallery/build/terminal/005.jpg

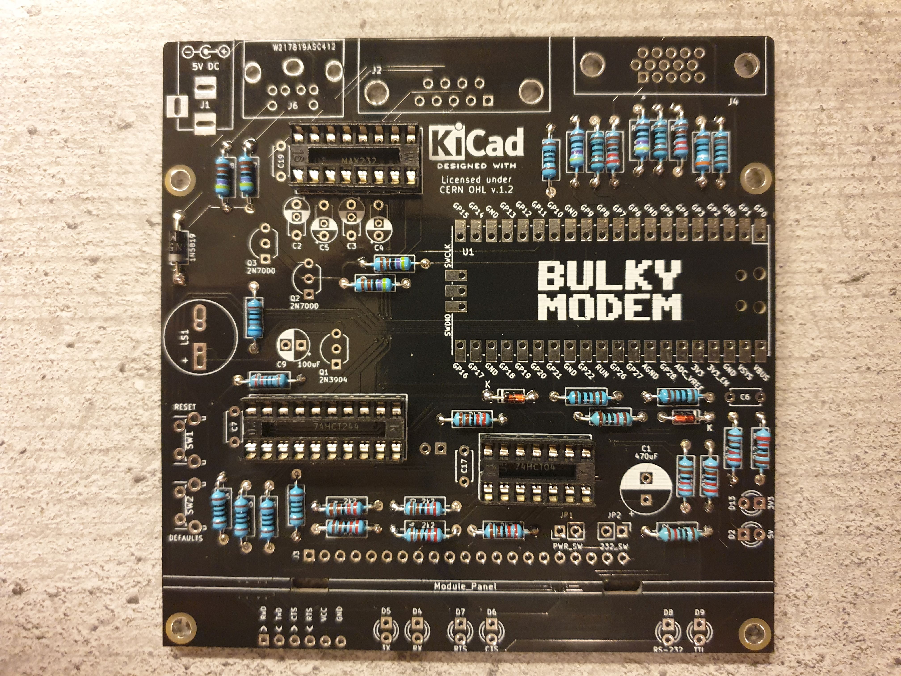
gallery/build/terminal/005.jpg
