tebl/BulkyModem/gallery/build/terminal/006.jpg

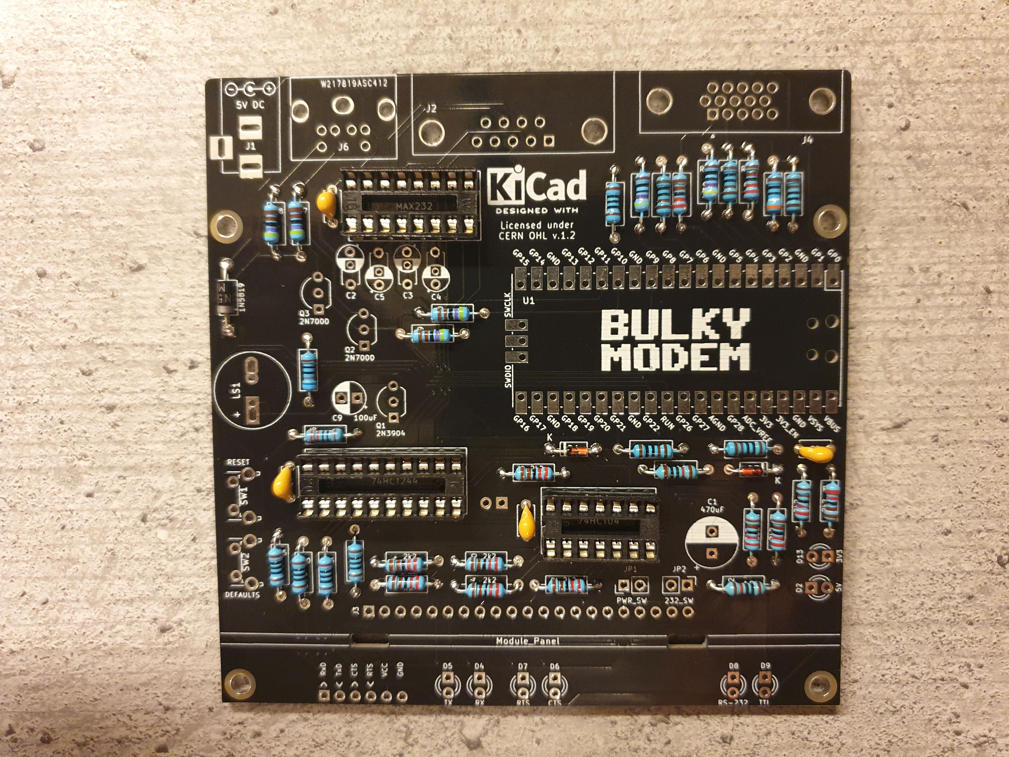
gallery/build/terminal/006.jpg
