tebl/BulkyModem/gallery/build/terminal/007.jpg

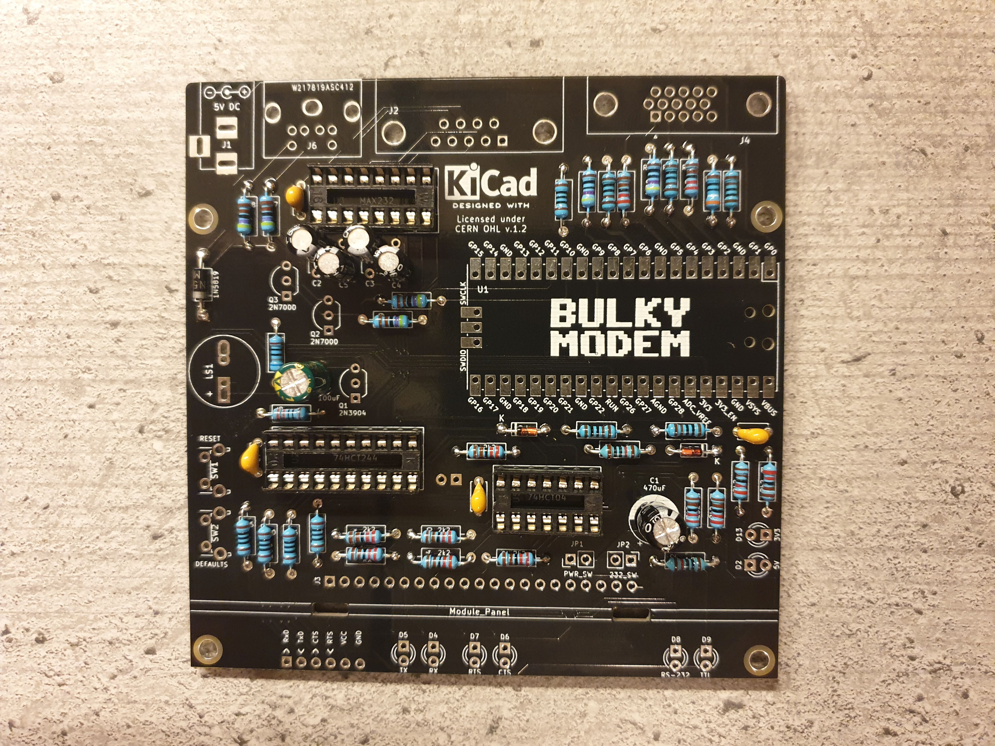
gallery/build/terminal/007.jpg
