tebl/BulkyModem/gallery/build/terminal/009.jpg

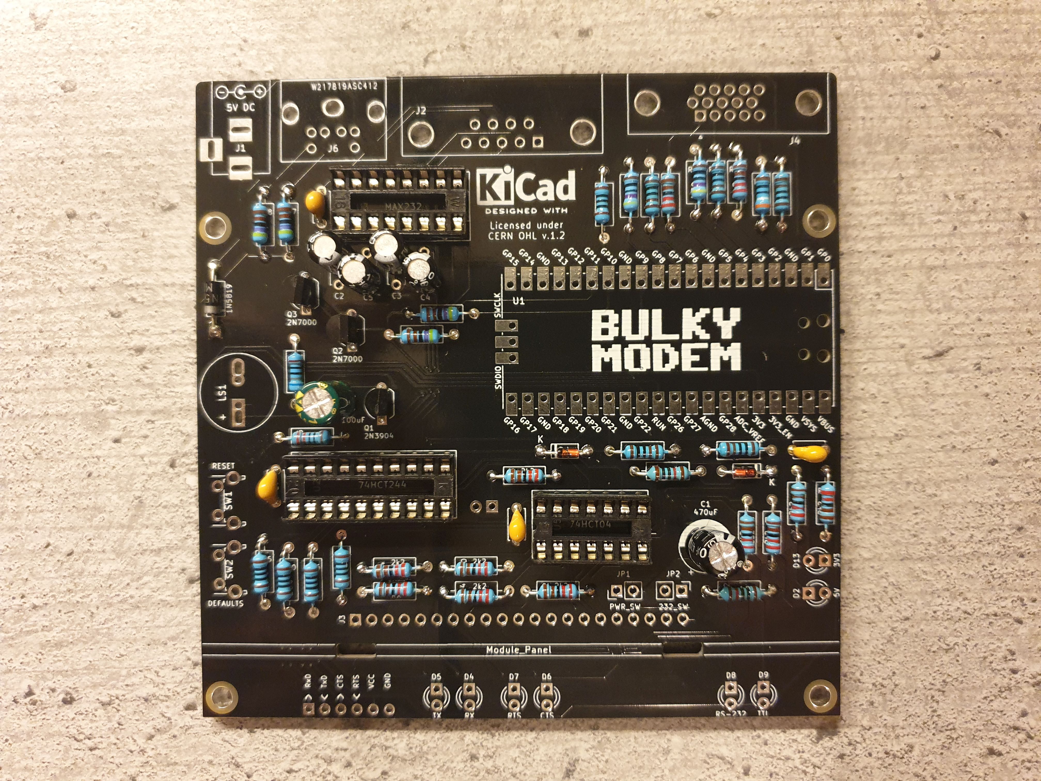
gallery/build/terminal/009.jpg
