tebl/BulkyModem/gallery/build/terminal/010.jpg

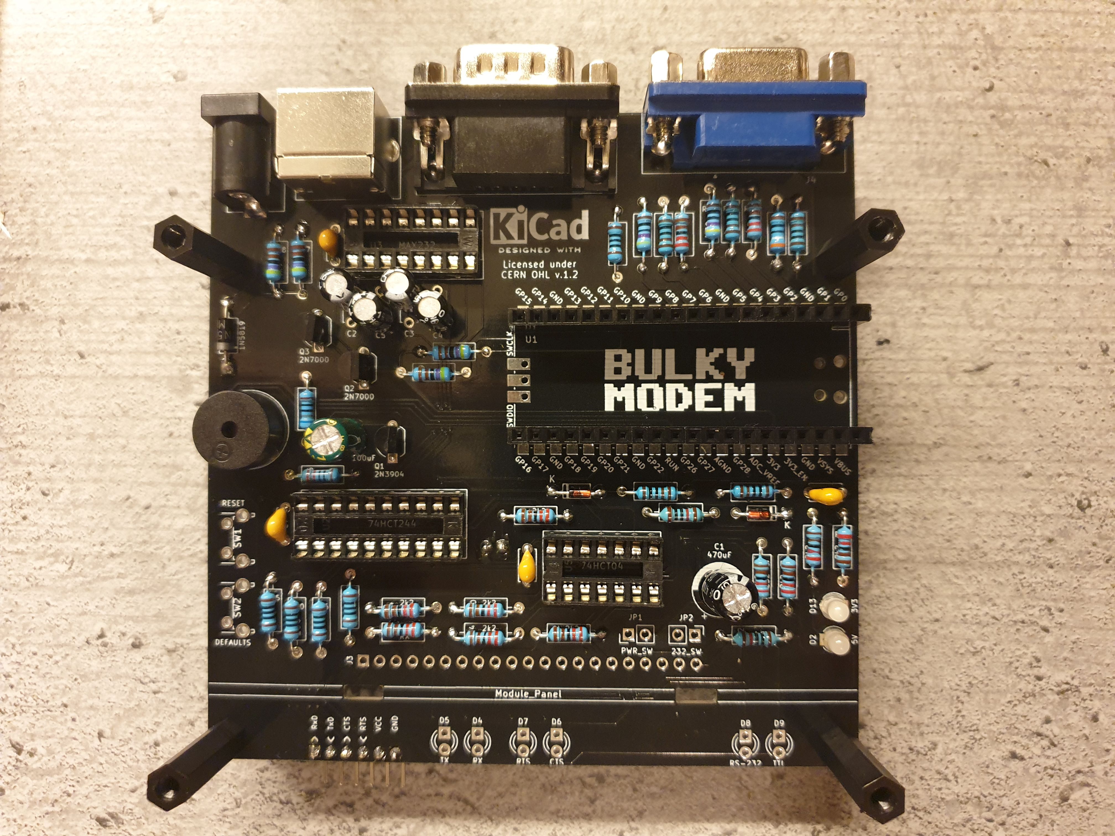
gallery/build/terminal/010.jpg
