tebl/BulkyModem/gallery/build/terminal/015.jpg

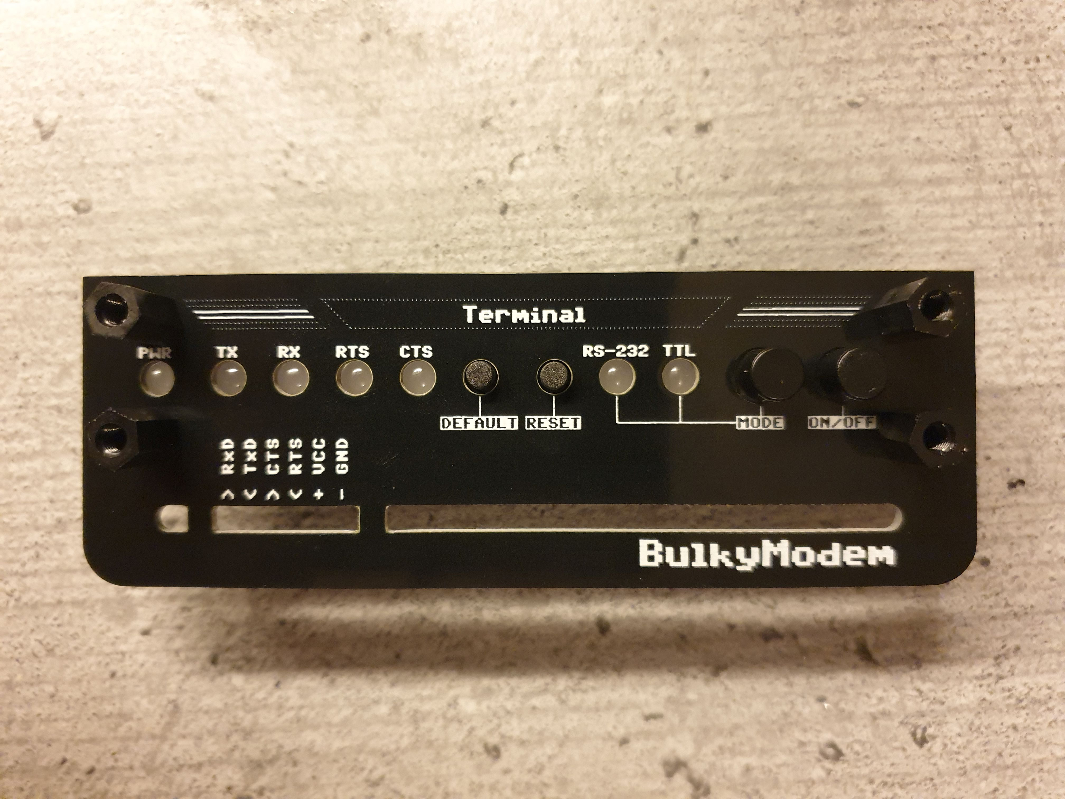
gallery/build/terminal/015.jpg
