tebl/BulkyModem/gallery/build/terminal/022.jpg

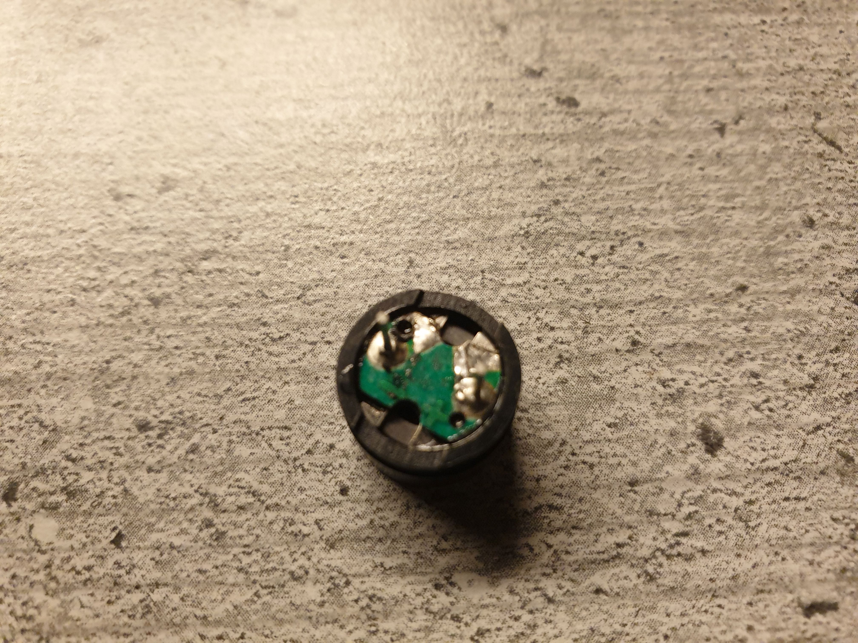
gallery/build/terminal/022.jpg
