tebl/BulkyModem/gallery/build/terminal/023.jpg

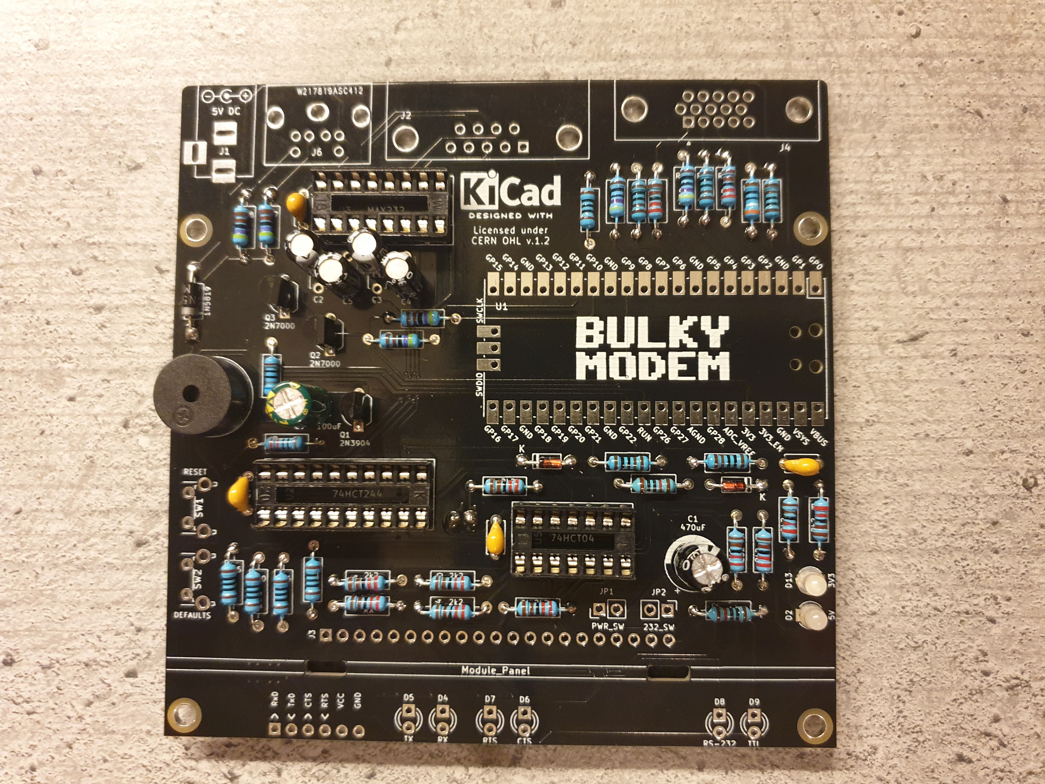
gallery/build/terminal/023.jpg
