tebl/BulkyModem/gallery/build/terminal/027.jpg

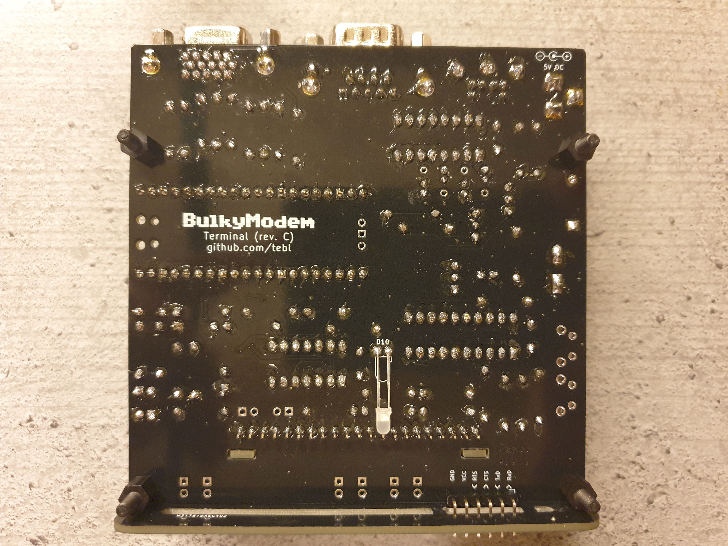
gallery/build/terminal/027.jpg
