tebl/BulkyModem/gallery/build/terminal/030.jpg

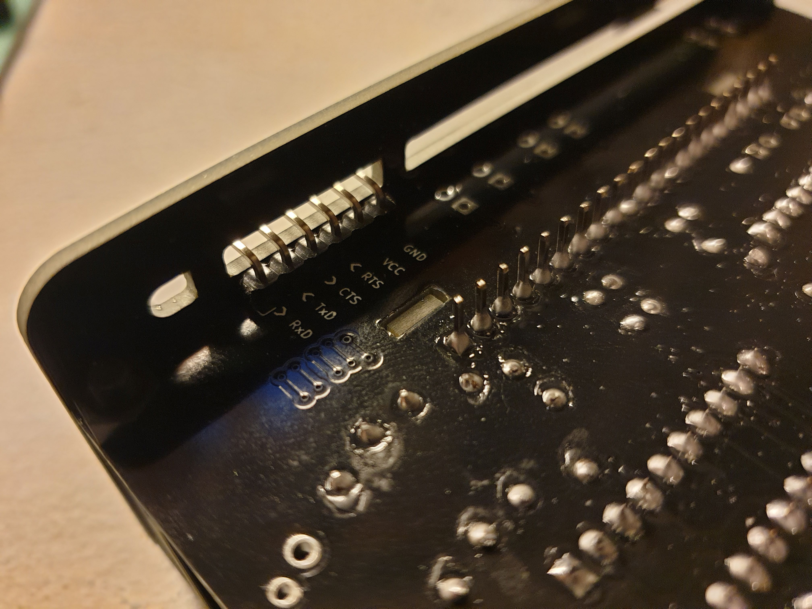
gallery/build/terminal/030.jpg
