tebl/BulkyModem/gallery/build/terminal/031.jpg

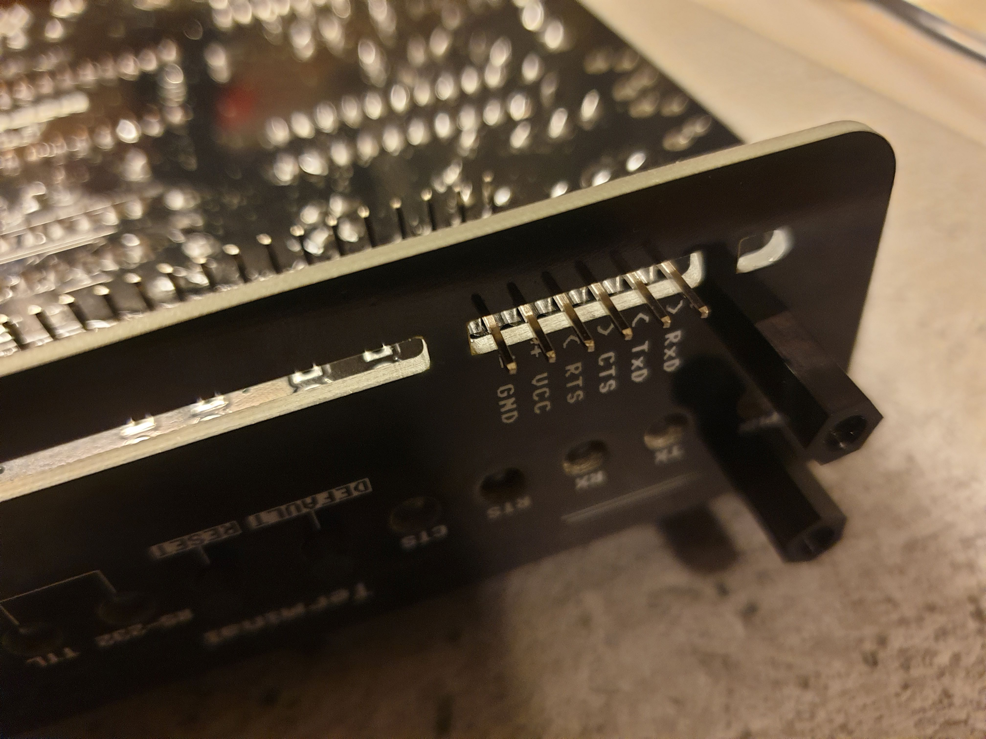
gallery/build/terminal/031.jpg
