tebl/BulkyModem/gallery/build/terminal/032.jpg

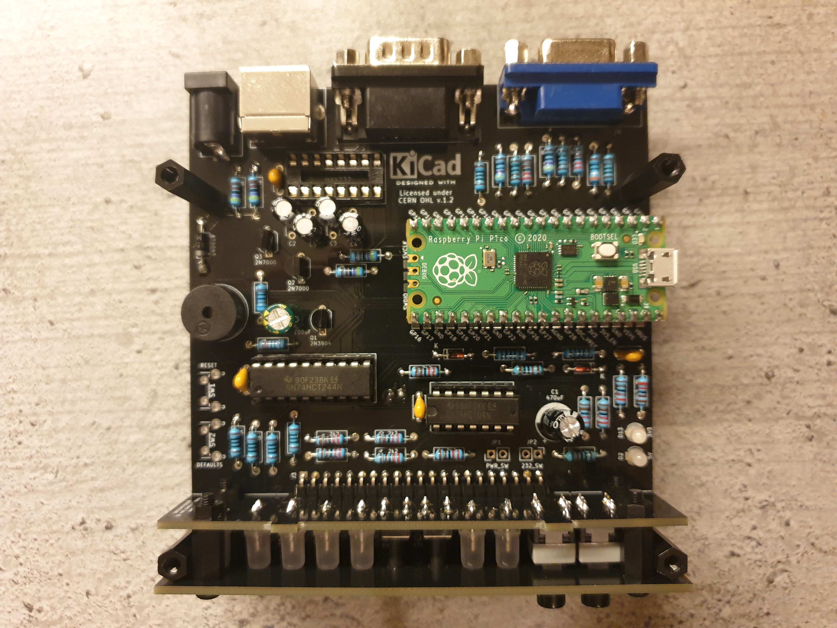
gallery/build/terminal/032.jpg
