tebl/BulkyModem/gallery/build/terminal/040.jpg

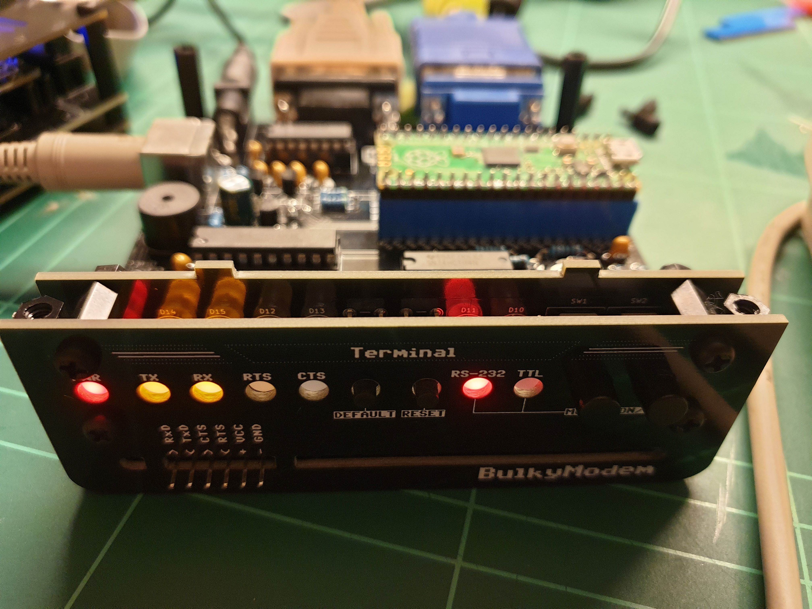
gallery/build/terminal/040.jpg
