tebl/BulkyModem/gallery/build/terminal/041.jpg

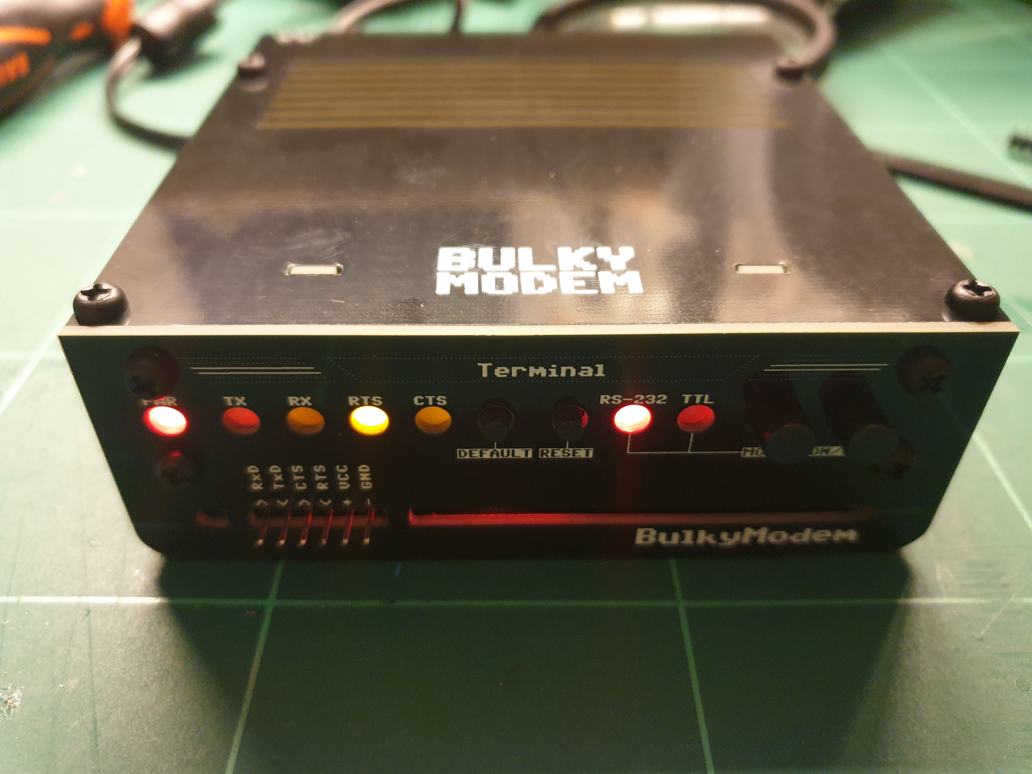
gallery/build/terminal/041.jpg
