tebl/BulkyModem/gallery/build/terminal/panel_002.jpg

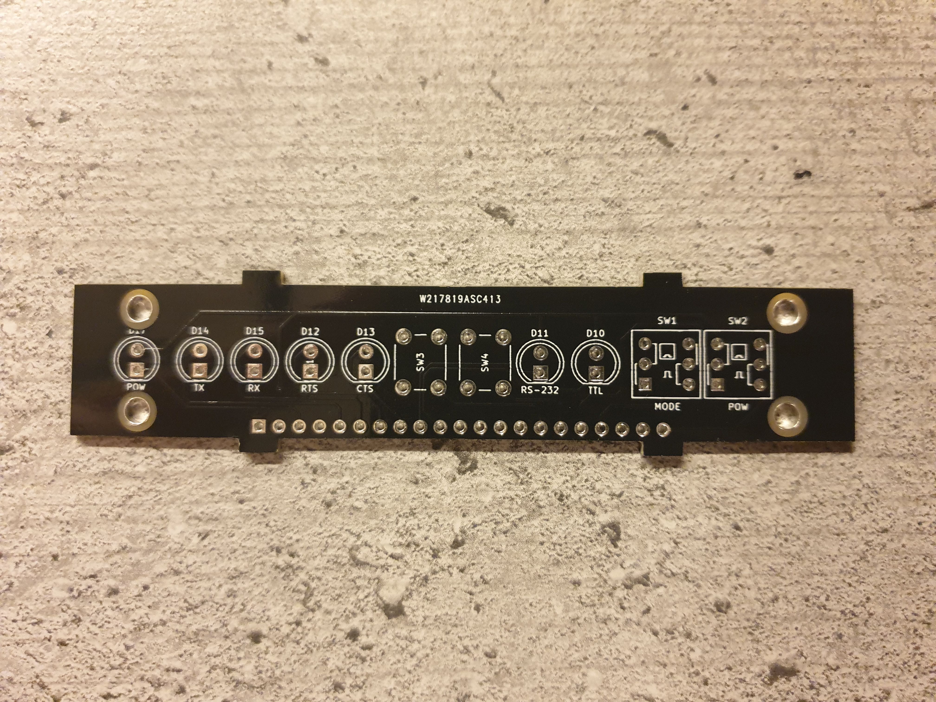
gallery/build/terminal/panel_002.jpg
