tebl/BulkyModem/gallery/build/terminal/panel_004.jpg

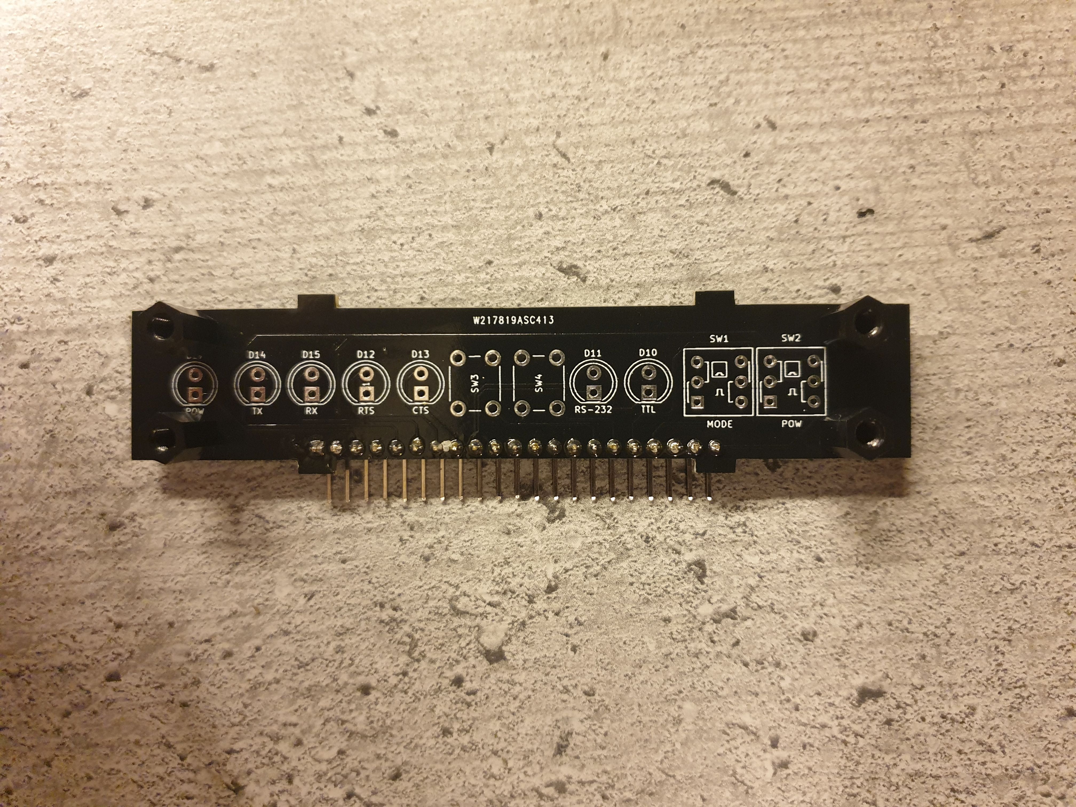
gallery/build/terminal/panel_004.jpg
