tebl/BulkyModem/gallery/build/terminal/panel_005.jpg

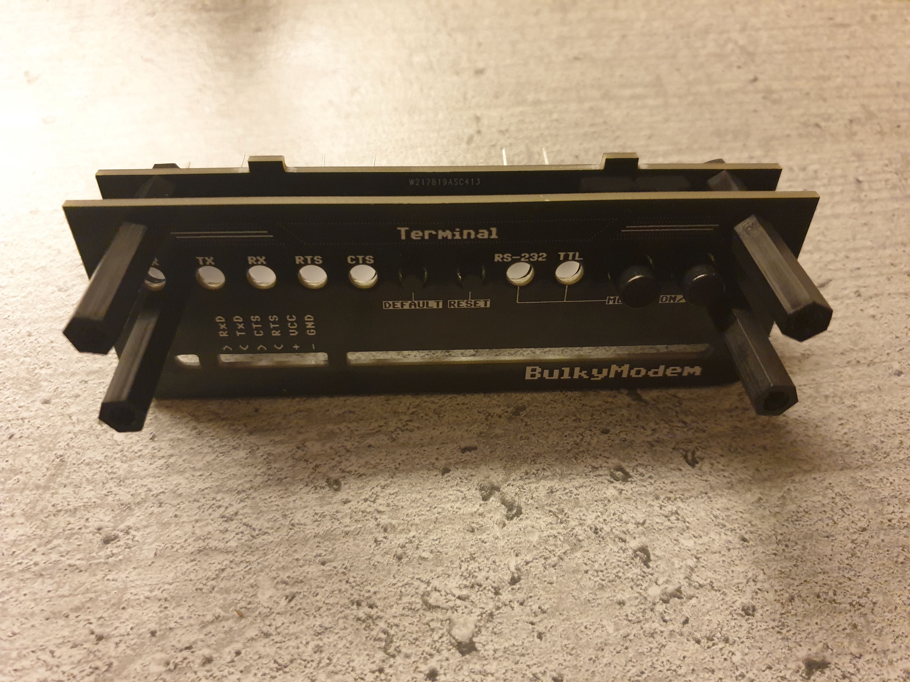
gallery/build/terminal/panel_005.jpg
