tebl/BulkyModem/gallery/build/terminal/panel_006.jpg

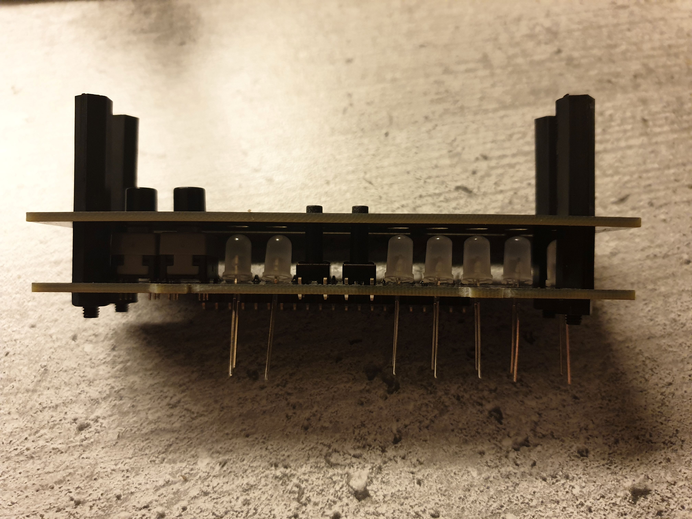
gallery/build/terminal/panel_006.jpg
