tebl/BulkyModem/gallery/build/terminal/panel_010.jpg

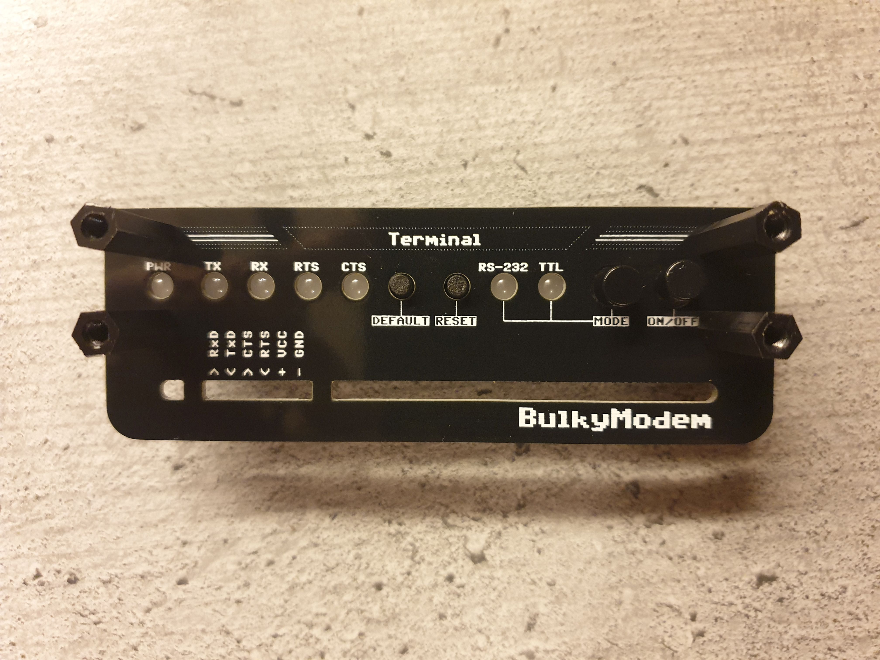
gallery/build/terminal/panel_010.jpg
