tebl/BulkyModem/documentation/schematic/faceplates/BulkyModem FP2.pdf

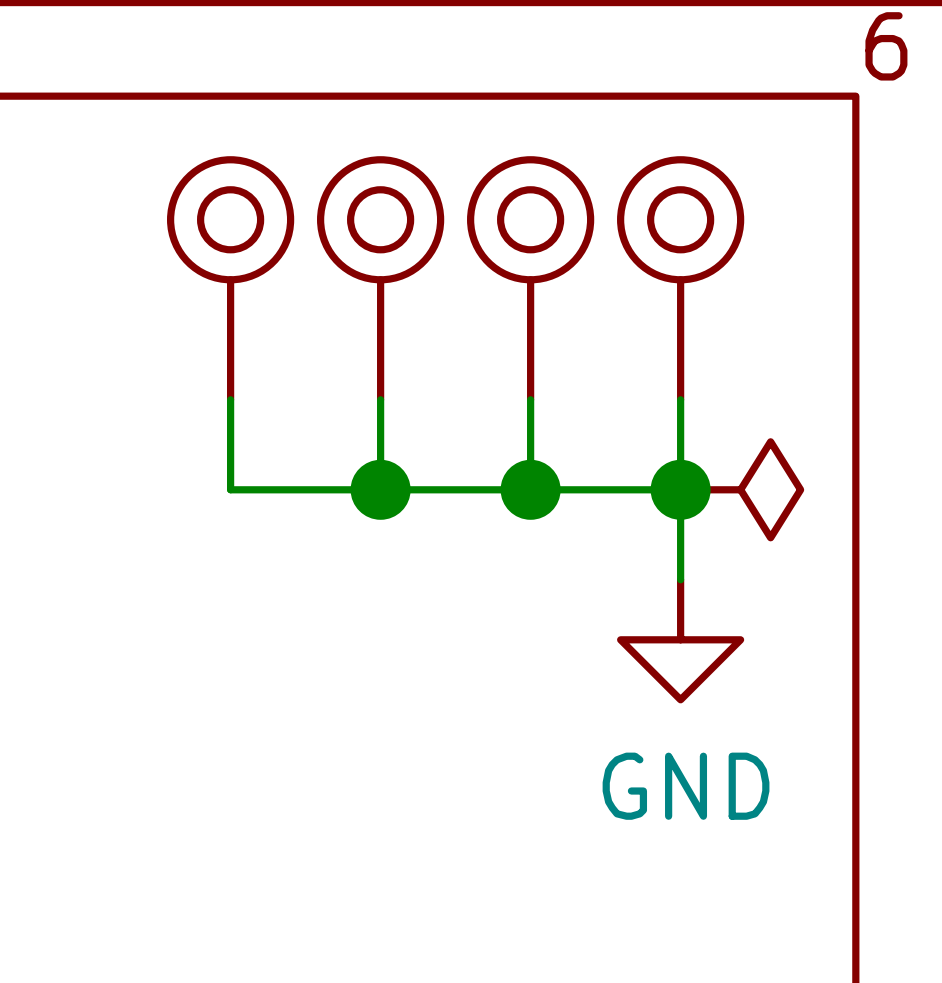
[picture p185: page 1]

A cosmetic plate to go on the front of the device.

Labels on the front should approximate those seen on USRobotics-modems, manual at:
File: BulkyModem FP2.sch Sheet: / https://support.usr.com/support/3453c/3453c-ug/viewing_leds.html

Id: 1/1 Title: BulkyModem Front Plate (FP2)
