tebl/BulkyModem/documentation/schematic/faceplates/BulkyModem FP1.pdf

A cosmetic plate to go on the front of the device.

Labels are the ports as seen by the modem, see FP2 or FP3 for something that doesn't
File: BulkyModem FP1.sch Sheet: / require quite as much in the way of mental mapping.

Id: 1/1 Title: BulkyModem Front Plate (FP1)
