tebl/BulkyModem/documentation/schematic/faceplates/BulkyModem Terminal FP3.pdf

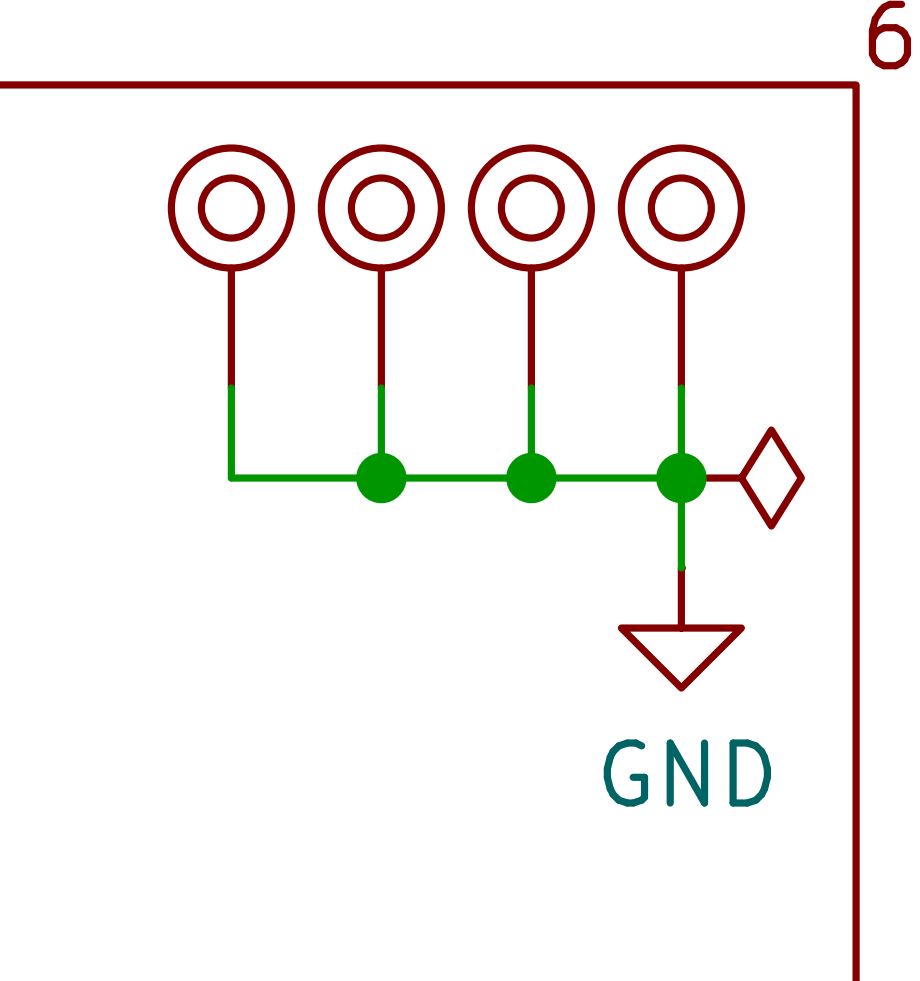
[picture p189: page 1]
