tebl/BulkyModem/documentation/schematic/faceplates/BulkyModem FP3.pdf

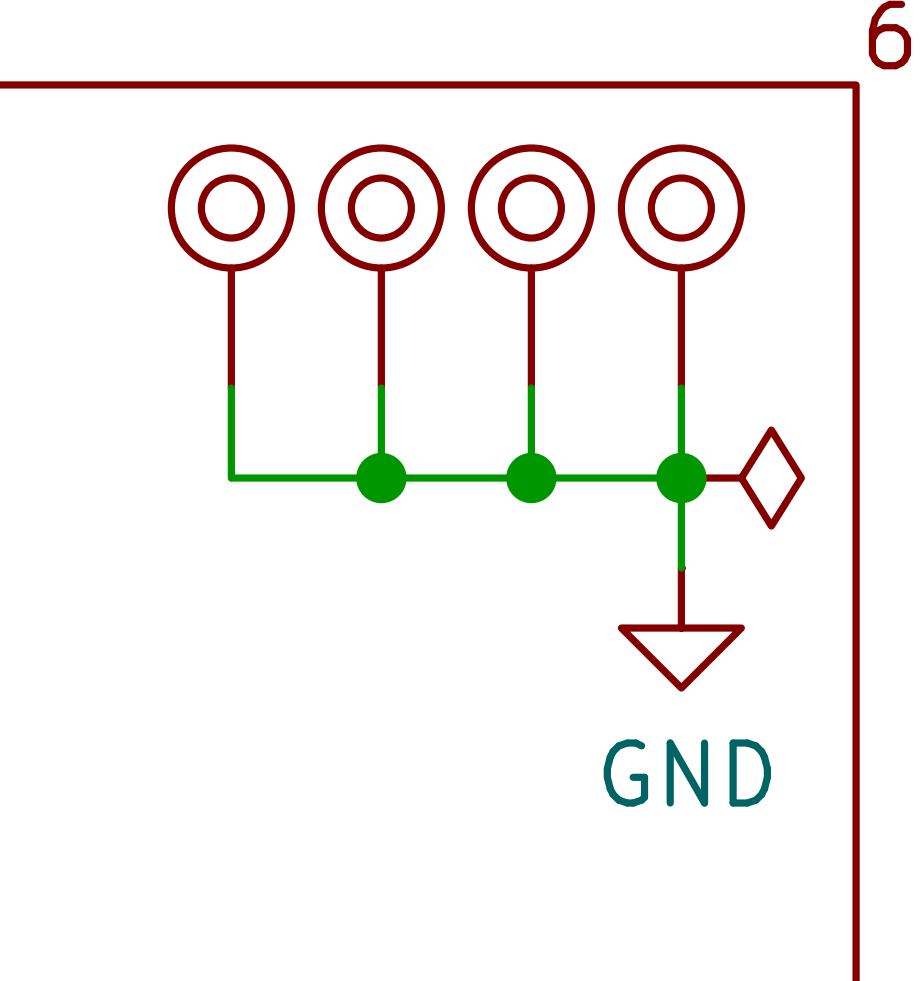
[picture p190: page 1]
