tebl/BulkyModem/BulkyModem UserPort Adapter/BulkyModem UserPort Adapter.kicad_pcb

## KiCad design BulkyModem UserPort Adapter/BulkyModem UserPort Adapter.kicad_pcb (2024-05-30)

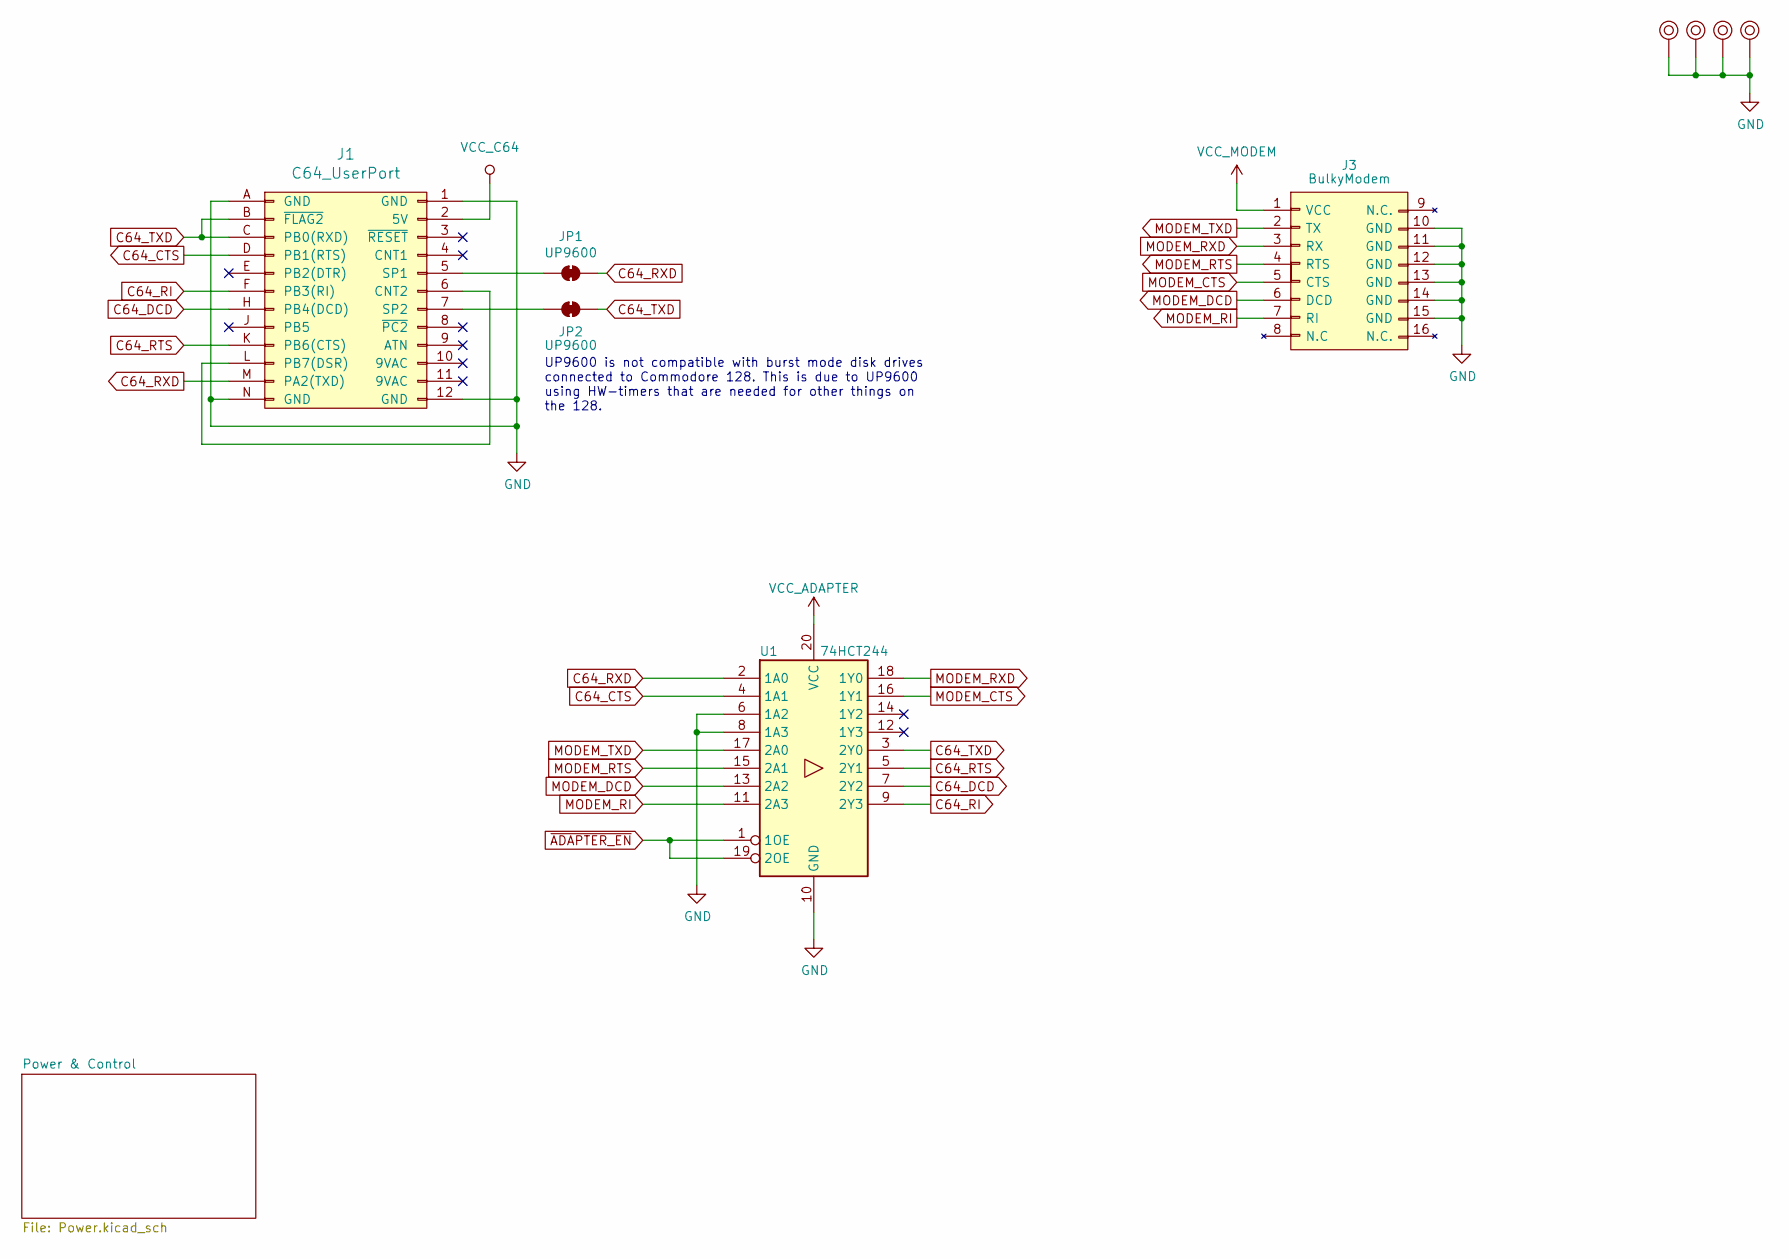
[picture p213: schematic BulkyModem UserPort Adapter.kicad_sch, BulkyModem (C64 UserPort Adapter)]

Parts:
J1: C64_UserPort; C64_User-Port
J3: BulkyModem; UserPort_Adapter_IDC
JP1, JP2: UP9600; PinHeader_1x02_P2.54mm_Vertical
M1, M2, M3, M4: Mounting; M3_pin
U1: 74HCT244; DIP-20_W7.62mm_Socket_LongPads

Connections:
C64_CTS: J1.D (PB1(RTS)), U1.4 (1A1)
C64_DCD: J1.H (PB4(DCD)), U1.7 (2Y2)
C64_RI: J1.F (PB3(RI)), U1.9 (2Y3)
C64_RTS: J1.K (PB6(CTS)), U1.5 (2Y1)
C64_RXD: J1.M (PA2(TXD)), JP1.2 (B), U1.2 (1A0)
C64_TXD: J1.B (~FLAG2), J1.C (PB0(RXD)), JP2.2 (B), U1.3 (2Y0)
GND: J1.1 (GND), J1.12 (GND), J1.A (GND), J1.N (GND), J3.10 (GND), J3.11 (GND), J3.12 (GND), J3.13 (GND), J3.14 (GND), J3.15 (GND), M1.1, M2.1, M3.1, M4.1, U1.6 (1A2), U1.8 (1A3), U1.10 (GND); also elsewhere on the board
MODEM_CTS: J3.5 (CTS), U1.16 (1Y1)
MODEM_DCD: J3.6 (DCD), U1.13 (2A2)
MODEM_RI: J3.7 (RI), U1.11 (2A3)
MODEM_RTS: J3.4 (RTS), U1.15 (2A1)
MODEM_RXD: J3.3 (RX), U1.18 (1Y0)
MODEM_TXD: J3.2 (TX), U1.17 (2A0)
unnamed: J1.6 (CNT2), J1.L (PB7(DSR))
unnamed: J1.5 (SP1), JP1.1 (A)
unnamed: J1.7 (SP2), JP2.1 (A)
VCC_ADAPTER: U1.20 (VCC); also elsewhere on the board
VCC_C64: J1.2 (5V); also elsewhere on the board
VCC_MODEM: J3.1 (VCC); also elsewhere on the board
~ADAPTER_EN: U1.1 (1OE), U1.19 (2OE); also elsewhere on the board

Notes on the sheet:
UP9600 is not compatible with burst mode disk drives connected to Commodore 128. This is due to UP9600 using HW-timers that are needed for other things on the 128.

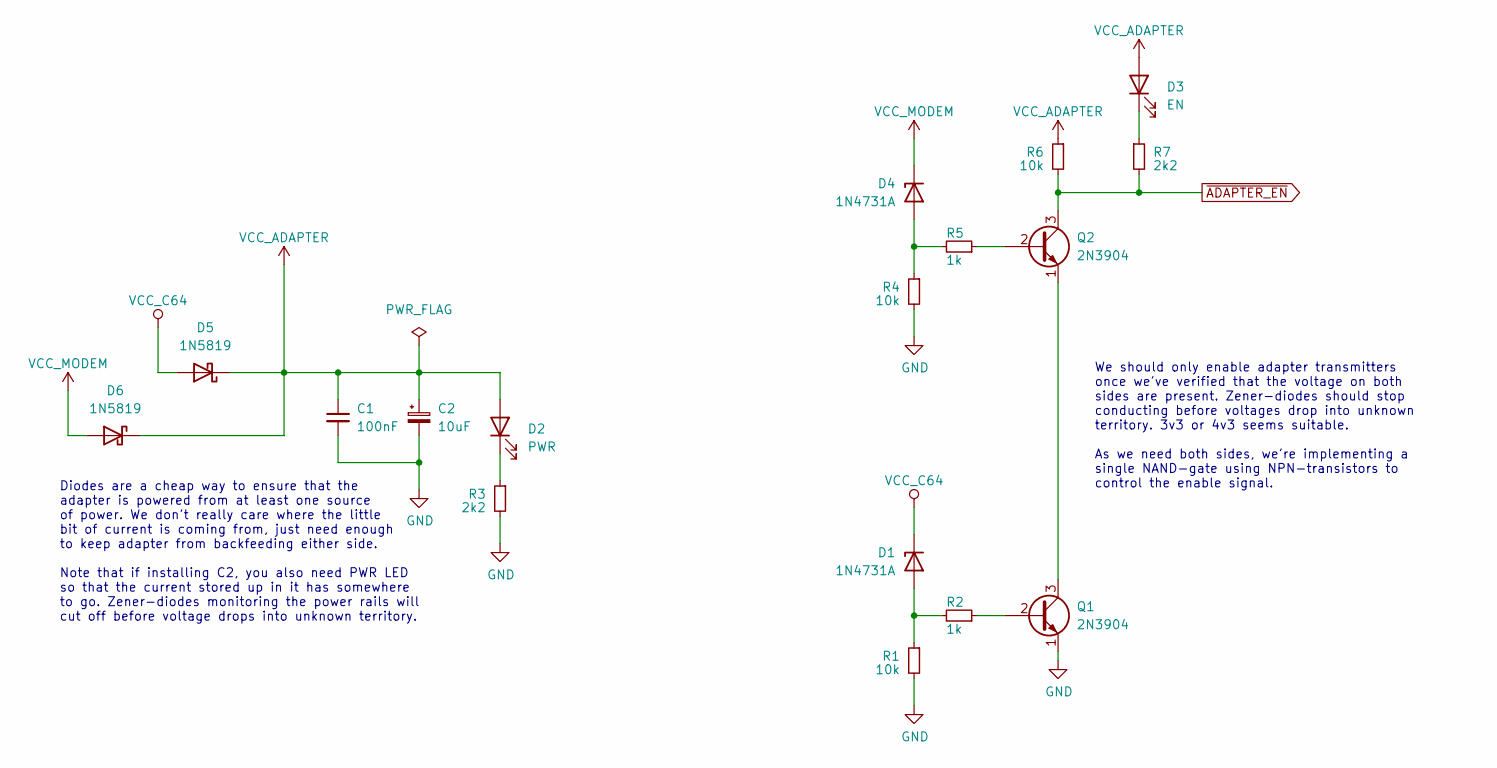
[picture p214: schematic Power.kicad_sch, Power and control]

Parts:
C1: 100nF; C_Disc_D4.7mm_W2.5mm_P5.00mm
C2: 10uF; CP_Radial_D4.0mm_P2.00mm
D1, D4: 1N4731A; D_DO-41_SOD81_P10.16mm_Horizontal
D2: PWR; LED_D3.0mm
D3: EN; LED_D3.0mm
D5, D6: 1N5819; D_DO-41_SOD81_P10.16mm_Horizontal
Q1, Q2: 2N3904; TO-92_Inline_Wide
R1, R4, R6: 10k; R_Axial_DIN0207_L6.3mm_D2.5mm_P10.16mm_Horizontal
R2, R5: 1k; R_Axial_DIN0207_L6.3mm_D2.5mm_P10.16mm_Horizontal
R3, R7: 2k2; R_Axial_DIN0207_L6.3mm_D2.5mm_P10.16mm_Horizontal

Connections:
GND: C1.2, C2.2, Q1.1 (E), R1.2, R3.2, R4.2; also elsewhere on the board
unnamed: D1.2 (A), R1.1, R2.2
unnamed: D2.1 (K), R3.1
unnamed: D3.1 (K), R7.1
unnamed: D4.2 (A), R4.1, R5.2
unnamed: Q1.2 (B), R2.1
unnamed: Q1.3 (C), Q2.1 (E)
unnamed: Q2.2 (B), R5.1
VCC_ADAPTER: C1.1, C2.1, D2.2 (A), D3.2 (A), D5.1 (K), D6.1 (K), R6.1; also elsewhere on the board
VCC_C64: D1.1 (K), D5.2 (A); also elsewhere on the board
VCC_MODEM: D4.1 (K), D6.2 (A); also elsewhere on the board
~ADAPTER_EN: Q2.3 (C), R6.2, R7.2; also elsewhere on the board

Notes on the sheet:
We should only enable adapter transmitters once we've verified that the voltage on both sides are present. Zener-diodes should stop conducting before voltages drop into unknown territory. 3v3 or 4v3 seems suitable. As we need both sides, we're implementing a single NAND-gate using NPN-transistors t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
Diodes are a cheap way to ensure that the adapter is powered from at least one source of power. We don't really care where the little bit of current is coming from, just need enough to keep adapter from backfeeding either side. Note that if installing C2, you also need PWR LED so that the current s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

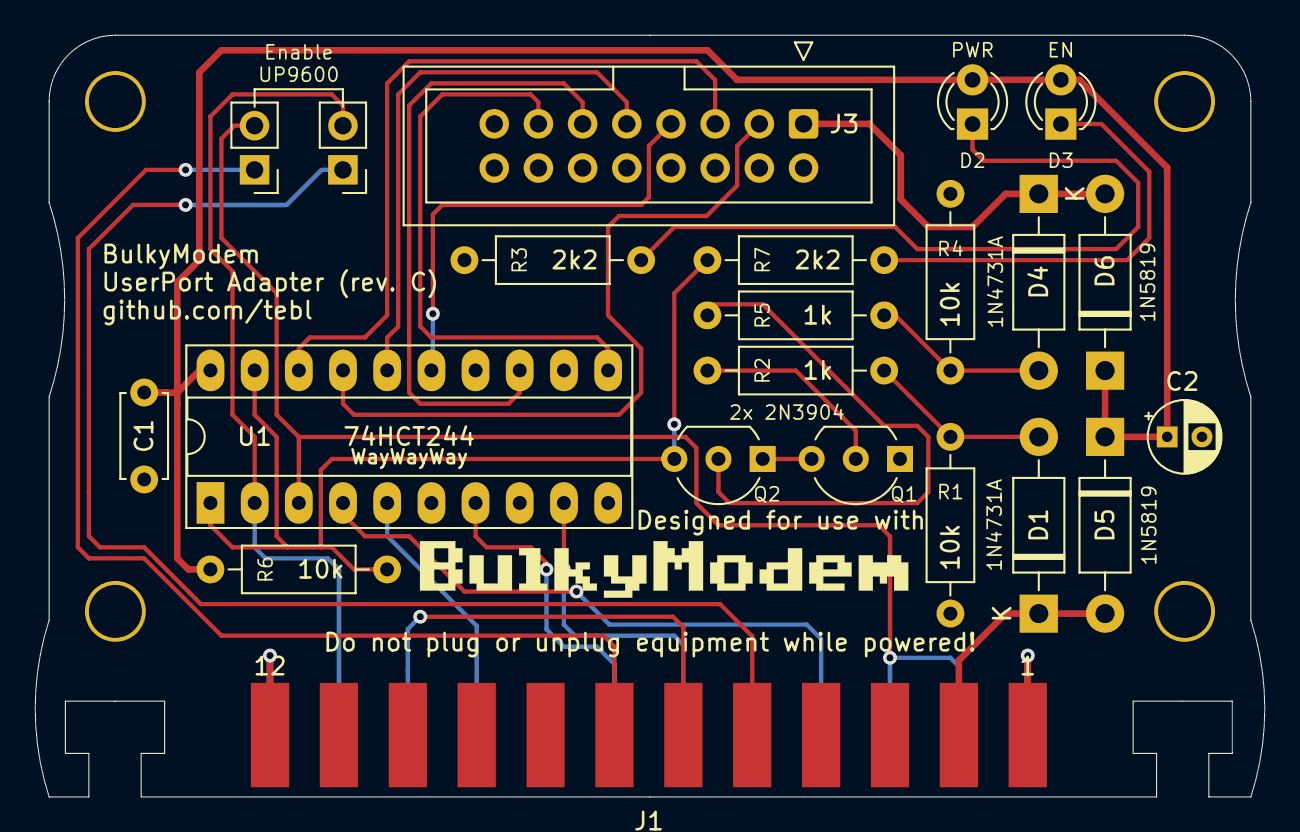
[picture p215: board BulkyModem UserPort Adapter.kicad_pcb from above]

Board: 2 copper layers, 70.7 x 43.8 mm, 26 parts (0 on the bottom side), 27 nets.
