tebl/BulkyModem/BulkyModem Module Audio/BulkyModem Module Audio.kicad_pcb

## KiCad design BulkyModem Module Audio/BulkyModem Module Audio.kicad_pcb (2024-05-28)

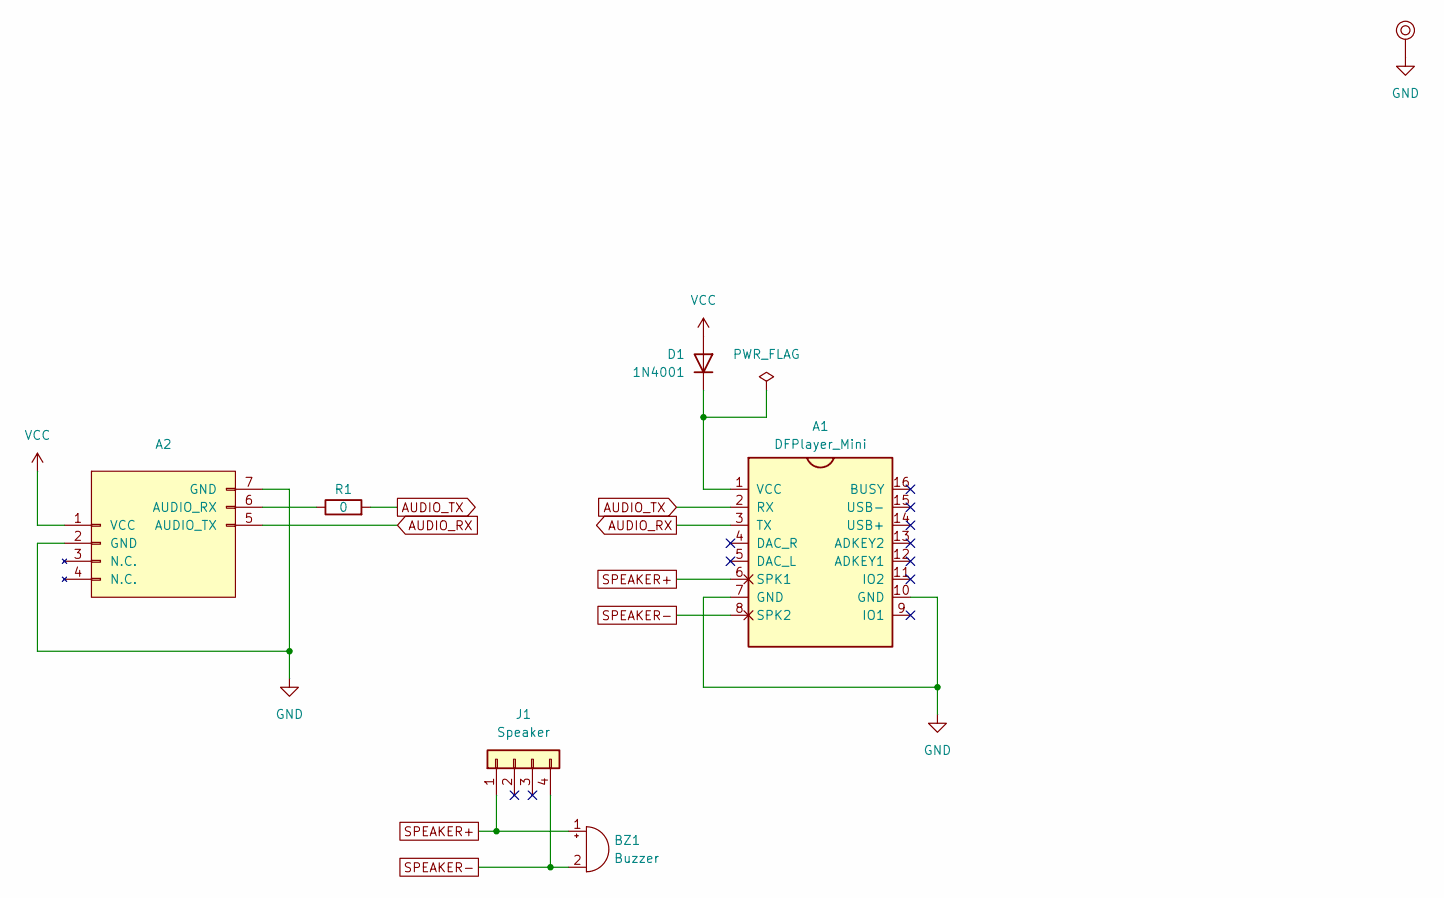
[picture p216: schematic BulkyModem Module Audio.kicad_sch, BulkyModem (Audio)]

Parts:
A1: DFPlayer_Mini
A2: AudioModule_Connector
BZ1: Buzzer; Buzzer_12x9.5RM7.6
D1: 1N4001; D_DO-41_SOD81_P10.16mm_Horizontal
J1: Speaker; PinHeader_1x04_P2.54mm_Horizontal
M1: Mounting_Pin; M3_pin
R1: 0; R_Axial_DIN0207_L6.3mm_D2.5mm_P10.16mm_Horizontal

Connections:
AUDIO_RX: A1.3 (TX), A2.5 (AUDIO_TX)
AUDIO_TX: A1.2 (RX), R1.2
GND: A1.7 (GND), A1.10 (GND), A2.2 (GND), A2.7 (GND), M1.1
unnamed: A1.1 (VCC), D1.1 (K)
unnamed: A2.6 (AUDIO_RX), R1.1
SPEAKER+: A1.6 (SPK1), BZ1.1 (+), J1.1
SPEAKER-: A1.8 (SPK2), BZ1.2 (-), J1.4
VCC: A2.1 (VCC), D1.2 (A)

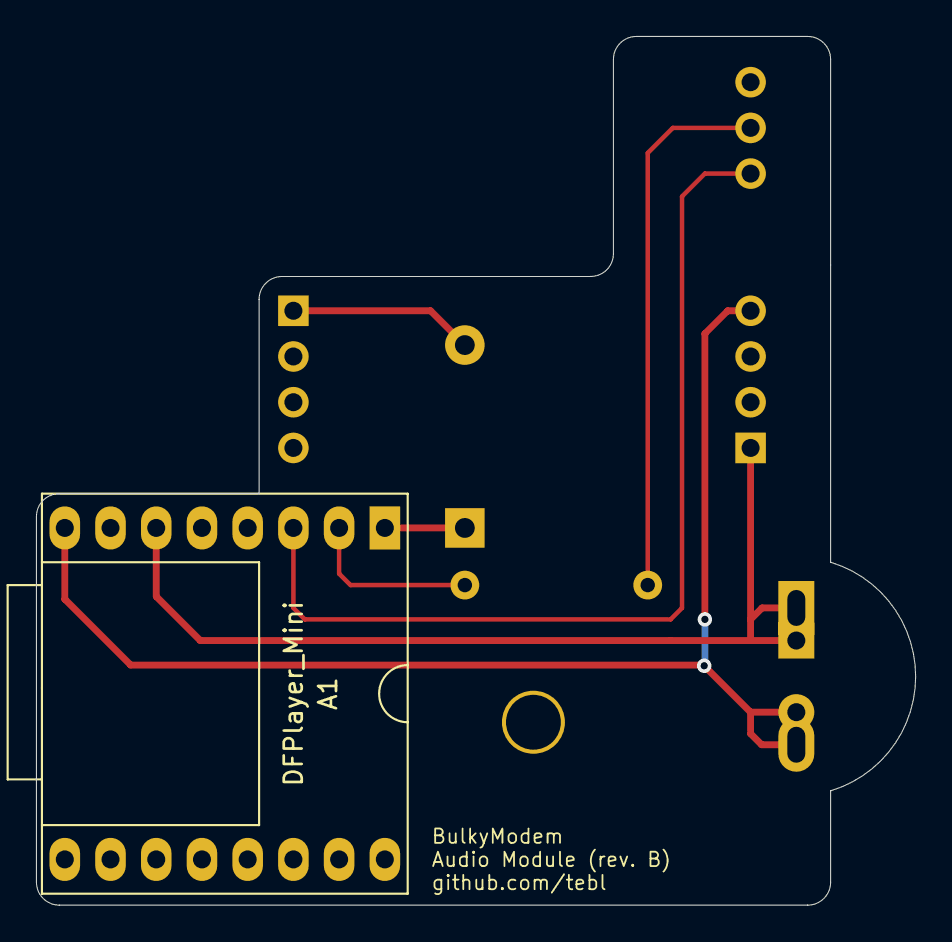
[picture p217: board BulkyModem Module Audio.kicad_pcb from above]

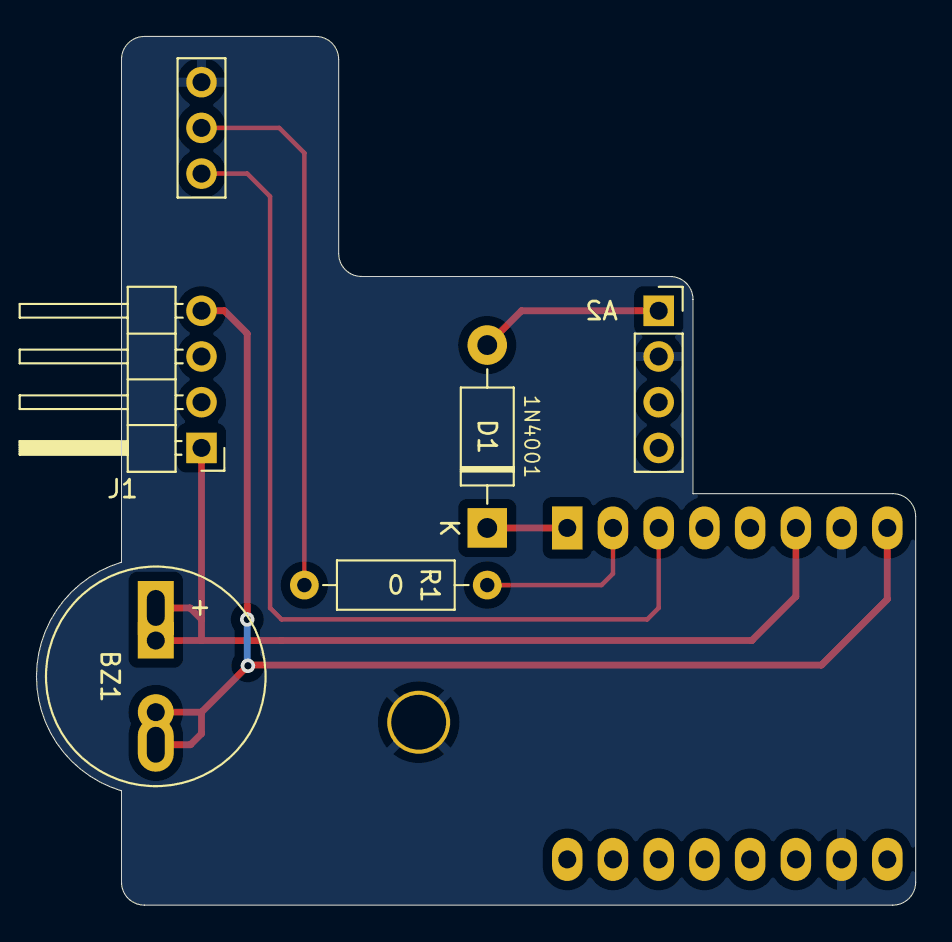
[picture p218: board BulkyModem Module Audio.kicad_pcb from below]

Board: 2 copper layers, 48.8 x 48.3 mm, 7 parts (4 on the bottom side), 8 nets.
