tebl/BulkyModem/gallery/build/mini32_rs232/003.jpg

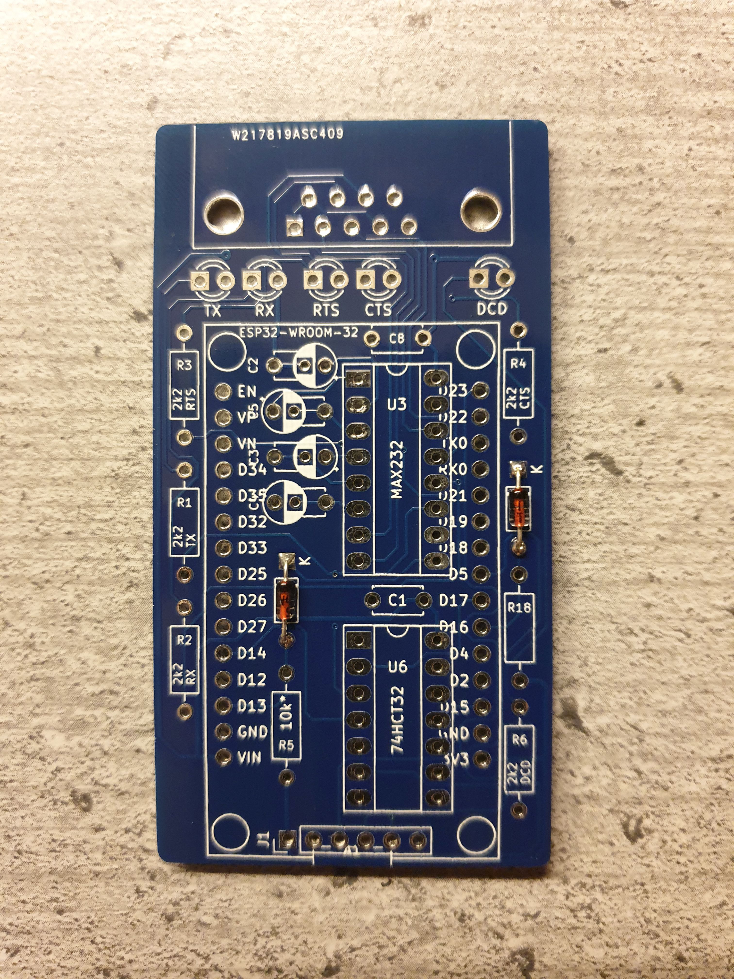
gallery/build/mini32_rs232/003.jpg
